Lancelotmay/BLETracker/src/ubx_messages_header.h

/***********************************************************
 *
 * Copyright (C) u-blox AG
 * u-blox AG, Thalwil, Switzerland
 *
 * All rights reserved.
 *
 * Permission to use, copy, modify, and distribute this software for any
 * purpose without fee is hereby granted, provided that this entire notice is
 * included in all copies of any software which is or includes a copy or
 * modification of this software and in all copies of the supporting
 * documentation for such software.
 *
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
 ***********************************************************
 *
 * Project:  Protocol Specification
 * Purpose:  Structure definitions for UBX messages
 * Audience: PUB
 *
 * This file is automatically generated!
 * Manual edits may be overwritten!
 *
 ***********************************************************/
/*!
	\file
	\brief UBX message definitions

*/

#ifndef __PROTO_UBX_STRUCT_DEF_H_479EEE3A_CC65683
#define __PROTO_UBX_STRUCT_DEF_H_479EEE3A_CC65683

#ifndef UBX_STANDARD_TYPES_DEFINED
/*----------------*/
/* Standard types */
/*----------------*/
typedef signed int			   I;   //!<  = I4
typedef unsigned int		   U;   //!<  = U4
typedef unsigned long		   BL;  //!<  = L4 (TRUE or FALSE only)
typedef	signed char			   I1;	//!<  signed 1 byte integer
typedef	signed short		   I2;	//!<  signed 2 byte integer
typedef	signed int			   I4;	//!<  signed 4 byte integer
typedef	signed long long int   I8;  //!<  signed 8 byte integer
typedef	unsigned char		   U1;	//!<  unsigned 1 byte integer
typedef	unsigned char		   X1;	//!<  unsigned 1 byte integer, to be interpreted as bitmask
typedef	unsigned short	       U2;	//!<  unsigned 2 byte integer
typedef	unsigned short		   X2;	//!<  unsigned 2 byte integer, to be interpreted as bitmask
typedef	unsigned int		   U4;	//!<  unsigned 4 byte integer
typedef	unsigned int		   X4;	//!<  unsigned 4 byte integer, to be interpreted as bitmask
typedef	unsigned long long int U8;	//!<  unsigned 8 byte integer
typedef	float				   R4;	//!<  4 byte floating point
typedef	double				   R8;	//!<  8 byte floating point
typedef	char				   CH;	//!<  ASCII character
typedef	unsigned char		   L1;	//!<  1 byte logical (TRUE or FALSE only)
typedef	unsigned short		   L2;	//!<  2 byte logical (TRUE or FALSE only)
typedef	unsigned int		   L4;	//!<  4 byte logical (TRUE or FALSE only)
typedef	unsigned int		    L;	//!<  4 byte logical (TRUE or FALSE only)

#define UBX_STANDARD_TYPES_DEFINED
#endif // ifndef UBX_STANDARD_TYPES_DEFINED

#ifndef TRUE
#define TRUE 1
#endif
#ifndef FALSE
#define FALSE 0
#endif

//! UBX Protocol Header
typedef struct UBX_HEAD_s
{
	U2 prefix;					//!< Prefix, always #UBX_PREFIX
	U1 class_id;					//!< UBX Class Id
	U1 msg_id;					//!< UBX Message Id
	U2 size;					//!< Payload Size
} UBX_HEAD_t, *UBX_HEAD_pt;

#define UBX_SYNC_CHAR_1 0xB5u    //!< First synchronization character of UBX Protocol
#define UBX_SYNC_CHAR_2 0x62u    //!< Second synchronization character of UBX Protocol
#define UBX_PREFIX      (UBX_SYNC_CHAR_2<<8|UBX_SYNC_CHAR_1) //!< UBX Protocol Prefix
#define UBX_PREFIX_SIZE 2u       //!< UBX Protocol Prefix Size in bytes
#define UBX_CHKSUM_SIZE 2u       //!< UBX Protocol Checksum Size in bytes

#define UBX_HEAD_SIZE sizeof(UBX_HEAD_t)                      //!< UBX Protocol Header Size
#define UBX_FRAME_SIZE (UBX_HEAD_SIZE+UBX_CHKSUM_SIZE) //!< Total size of the UBX Frame



//================================================================
//! ACK_ACK_DATA0: Output
/*!
Message Acknowledged
Output upon processing of an input message


This message's id is #UBXID_ACK_ACK
*/
//================================================================

typedef struct UBX_ACK_ACK_DATA0_s
{
	U1  clsID;                    //!< Class ID of the Acknowledged Message
	U1  msgID;                    //!< Message ID of the Acknowledged Message

} UBX_ACK_ACK_DATA0_t, *UBX_ACK_ACK_DATA0_pt;


#define UBXID_ACK_ACK 0x0501 //!< message id for ACK-ACK
	

//================================================================
//! ACK_NAK_DATA0: Output
/*!
Message Not-Acknowledged
Output upon processing of an input message


This message's id is #UBXID_ACK_NAK
*/
//================================================================

typedef struct UBX_ACK_NAK_DATA0_s
{
	U1  clsID;                    //!< Class ID of the Not-Acknowledged Message
	U1  msgID;                    //!< Message ID of the Not-Acknowledged Message

} UBX_ACK_NAK_DATA0_t, *UBX_ACK_NAK_DATA0_pt;


#define UBXID_ACK_NAK 0x0500 //!< message id for ACK-NAK
	

//================================================================
//! AID_ALM_POLL0: Poll Request
/*!
Poll GPS Aiding Almanac Data
Poll GPS Aiding Data (Almanac) for all 32 SVs by sending this message to the receiver without any payload. The receiver will return 32 messages of type AID-ALM as defined below.

   \note: All UBX-AID messages are deprecated; use UBX-MGA messages instead

This message's id is #UBXID_AID_ALM
*/
//================================================================

typedef struct UBX_AID_ALM_POLL0_s
{

} UBX_AID_ALM_POLL0_t, *UBX_AID_ALM_POLL0_pt;


#define UBXID_AID_ALM 0x0B30 //!< message id for AID-ALM
	

//================================================================
//! AID_ALM_POLLID: Poll Request
/*!
Poll GPS Aiding Almanac Data for a SV
Poll GPS Aiding Data (Almanac) for an SV by sending this message to the receiver. The receiver will return one message of type AID-ALM as defined below.

   \note: All UBX-AID messages are deprecated; use UBX-MGA messages instead

This message's id is #UBXID_AID_ALM
*/
//================================================================

typedef struct UBX_AID_ALM_POLLID_s
{
	U1  svid;                     //!< SV ID for which the receiver shall return its Almanac Data (Valid Range: 1 .. 32 or 51, 56, 63).

} UBX_AID_ALM_POLLID_t, *UBX_AID_ALM_POLLID_pt;


//#define UBXID_AID_ALM 0x0B30  // already defined, see above


//================================================================
//! AID_ALM_DATA0: Input/Output
/*!
GPS Aiding Almanac Input/Output Message
* If the WEEK Value is 0, DWRD0 to DWRD7 are not sent as the Almanac is not available for the given SV. This may happen even if NAV-SVINFO and RXM-SVSI are indicating almanac availability as the internal data may not represent the content of an original broadcast almanac (or only parts thereof).
* DWORD0 to DWORD7 contain the 8 words following the Hand-Over Word ( HOW ) from the GPS navigation message, either pages 1 to 24 of sub-frame 5 or pages 2 to 10 of subframe 4. See IS-GPS-200 for a full description of the contents of the Almanac pages.
* In DWORD0 to DWORD7, the parity bits have been removed, and the 24 bits of data are located in Bits 0 to 23. Bits 24 to 31 shall be ignored.
* Example: Parameter e (Eccentricity) from Almanac Subframe 4/5, Word 3, Bits 69-84 within the subframe can be found in DWRD0, Bits 15-0 whereas Bit 0 is the LSB.

   \note: All UBX-AID messages are deprecated; use UBX-MGA messages instead

This message's id is #UBXID_AID_ALM
*/
//================================================================

typedef struct UBX_AID_ALM_DATA0_s
{
	U4  svid;                     //!< SV ID for which this
	U4  week;                     //!< Issue Date of Almanac (GPS week number)
	//OPTIONAL: UBX_AID_ALM_DATA0_DWRD_t repeat0[0];              

} UBX_AID_ALM_DATA0_t, *UBX_AID_ALM_DATA0_pt;


//! Repeated Sub-Structure of #UBX_AID_ALM_DATA0_t
typedef struct UBX_AID_ALM_DATA0_DWRD_s
{
	U4  dwrd[8];                  //!< Almanac Words

} UBX_AID_ALM_DATA0_DWRD_t, *UBX_AID_ALM_DATA0_DWRD_pt;



//#define UBXID_AID_ALM 0x0B30  // already defined, see above


//================================================================
//! AID_AOP_POLL0: Poll Request
/*!
Poll AssistNow Autonomous data, all satellites
Poll <i>AssistNow Autonomous</i> aiding data for all GPS satellites by sending this empty message. The receiver will return an AID-AOP message (see definition below) for each GPS satellite for which data is available.

   \note: All UBX-AID messages are deprecated; use UBX-MGA messages instead

This message's id is #UBXID_AID_AOP
*/
//================================================================

typedef struct UBX_AID_AOP_POLL0_s
{

} UBX_AID_AOP_POLL0_t, *UBX_AID_AOP_POLL0_pt;


#define UBXID_AID_AOP 0x0B33 //!< message id for AID-AOP
	

//================================================================
//! AID_AOP_POLLID: Poll Request
/*!
Poll AssistNow Autonomous data, one GPS satellite
Poll the <i>AssistNow Autonomous</i> data for the specified GPS satellite. The receiver will return a AID-AOP message (see definition below) if data is available for the requested satellite.

   \note: All UBX-AID messages are deprecated; use UBX-MGA messages instead

This message's id is #UBXID_AID_AOP
*/
//================================================================

typedef struct UBX_AID_AOP_POLLID_s
{
	U1  svid;                     //!< GPS SV ID for which the data is requested (valid range: 1..32).

} UBX_AID_AOP_POLLID_t, *UBX_AID_AOP_POLLID_pt;


//#define UBXID_AID_AOP 0x0B33  // already defined, see above


//================================================================
//! AID_AOP_DATA2: Input/Output
/*!
AssistNow Autonomous data
If enabled, this message is output at irregular intervals. It is output whenever <i>AssistNow Autonomous</i> has produced new data for a satellite. Depending on the availability of the optional data the receiver will output either version of the message. If this message is polled using one of the two poll requests described above the receiver will send this message if AssistNow Autonomous data is available or the corresponding poll request message if no AssistNow Autonomous data is available for each satellite (i.e. svid 1..32). At the user's choice the optional data may be chopped from the payload of a previously polled message when sending the message back to the receiver. Sending a valid AID-AOP message to the receiver will automatically enable the <i>AssistNow Autonomous</i> feature on the receiver. See the section <r href=\"AOP-DESC'>AssistNow Autonomous</r> in the receiver description for details on this feature.

   \note: All UBX-AID messages are deprecated; use UBX-MGA messages instead

This message's id is #UBXID_AID_AOP
*/
//================================================================

typedef struct UBX_AID_AOP_DATA2_s
{
	U1  gnssId;                   //!< GNSS identifier (see <r href=\"DESC-SVNumbering-UBX'>Satellite Numbering</r>)
	U1  svId;                     //!< Satellite identifier (see <r href=\"DESC-SVNumbering-UBX'>Satellite Numbering</r>)
	U1  reserved1[2];             //!< <r href='DESC-UBX-Reserved'>Reserved</r>
	U1  data[64];                 //!< assistance data

} UBX_AID_AOP_DATA2_t, *UBX_AID_AOP_DATA2_pt;


//#define UBXID_AID_AOP 0x0B33  // already defined, see above


//================================================================
//! AID_EPH_POLL0: Poll Request
/*!
Poll GPS Aiding Ephemeris Data
Poll GPS Aiding Data (Ephemeris) for all 32 SVs by sending this message to the receiver without any payload. The receiver will return 32 messages of type AID-EPH as defined below.

   \note: All UBX-AID messages are deprecated; use UBX-MGA messages instead

This message's id is #UBXID_AID_EPH
*/
//================================================================

typedef struct UBX_AID_EPH_POLL0_s
{

} UBX_AID_EPH_POLL0_t, *UBX_AID_EPH_POLL0_pt;


#define UBXID_AID_EPH 0x0B31 //!< message id for AID-EPH
	

//================================================================
//! AID_EPH_POLLID: Poll Request
/*!
Poll GPS Aiding Ephemeris Data for a SV
Poll GPS Constellation Data (Ephemeris) for an SV by sending this message to the receiver. The receiver will return one message of type AID-EPH as defined below.

   \note: All UBX-AID messages are deprecated; use UBX-MGA messages instead

This message's id is #UBXID_AID_EPH
*/
//================================================================

typedef struct UBX_AID_EPH_POLLID_s
{
	U1  svid;                     //!< SV ID for which the receiver shall return its Ephemeris Data (Valid Range: 1 .. 32).

} UBX_AID_EPH_POLLID_t, *UBX_AID_EPH_POLLID_pt;


//#define UBXID_AID_EPH 0x0B31  // already defined, see above


//================================================================
//! AID_EPH_DATA0: Input/Output
/*!
GPS Aiding Ephemeris Input/Output Message
* SF1D0 to SF3D7 is only sent if ephemeris is available for this SV. If not, the payload may be reduced to 8 Bytes, or all bytes are set to zero, indicating that this SV Number does not have valid ephemeris for the moment. This may happen even if NAV-SVINFO and RXM-SVSI are indicating ephemeris availability as the internal data may not represent the content of an original broadcast ephemeris (or only parts thereof).
* SF1D0 to SF3D7 contain the 24 words following the Hand-Over Word ( HOW ) from the GPS navigation message, subframes 1 to 3. The Truncated TOW Count is not valid and cannot be used. See IS-GPS-200 for a full description of the contents of the Subframes.
* In SF1D0 to SF3D7, the parity bits have been removed, and the 24 bits of data are located in Bits 0 to 23. Bits 24 to 31 shall be ignored.
* When polled, the data contained in this message does not represent the full original ephemeris broadcast. Some fields that are irrelevant to u-blox receivers may be missing. The week number in Subframe 1 has already been modified to match the Time Of Ephemeris (TOE).

   \note: All UBX-AID messages are deprecated; use UBX-MGA messages instead

This message's id is #UBXID_AID_EPH
*/
//================================================================

typedef struct UBX_AID_EPH_DATA0_s
{
	U4  svid;                     //!< SV ID for which this ephemeris data is (Valid Range: 1 .. 32).
	U4  how;                      //!< Hand-Over Word of first Subframe. This is required if data is sent to the receiver.
	//OPTIONAL: UBX_AID_EPH_DATA0_SF1D_t repeat0[0];              

} UBX_AID_EPH_DATA0_t, *UBX_AID_EPH_DATA0_pt;


//! Repeated Sub-Structure of #UBX_AID_EPH_DATA0_t
typedef struct UBX_AID_EPH_DATA0_SF1D_s
{
	U4  sf1d[8];                  //!< Subframe 1 Words 3..10 (SF1D0..SF1D7)
	U4  sf2d[8];                  //!< Subframe 2 Words 3..10 (SF2D0..SF2D7)
	U4  sf3d[8];                  //!< Subframe 3 Words 3..10 (SF3D0..SF3D7)

} UBX_AID_EPH_DATA0_SF1D_t, *UBX_AID_EPH_DATA0_SF1D_pt;



//#define UBXID_AID_EPH 0x0B31  // already defined, see above


//================================================================
//! AID_HUI_POLL0: Poll Request
/*!
Poll GPS Health, UTC, ionosphere parameters
-

   \note: All UBX-AID messages are deprecated; use UBX-MGA messages instead

This message's id is #UBXID_AID_HUI
*/
//================================================================

typedef struct UBX_AID_HUI_POLL0_s
{

} UBX_AID_HUI_POLL0_t, *UBX_AID_HUI_POLL0_pt;


#define UBXID_AID_HUI 0x0B02 //!< message id for AID-HUI
	

//================================================================
//! AID_HUI_DATA1: Input/Output
/*!
GPS Health, UTC and ionosphere parameters
This message contains a health bit mask, UTC time and Klobuchar parameters. For more information on these parameters, see the ICD-GPS-200 documentation.

   \note: All UBX-AID messages are deprecated; use UBX-MGA messages instead

This message's id is #UBXID_AID_HUI
*/
//================================================================

typedef struct UBX_AID_HUI_DATA1_s
{
	X4  health;                   //!< Bitmask, every bit represenst a GPS SV (1-32). If the bit is set the SV is healthy.
	R8  utcA0;                    //!< UTC - parameter A0
	R8  utcA1;                    //!< UTC - parameter A1
	I4  utcTOW;                   //!< UTC - reference time of week
	I2  utcWNT;                   //!< UTC - reference week number
	I2  utcLS;                    //!< UTC - time difference due to leap seconds before event
	I2  utcWNF;                   //!< UTC - week number when next leap second event occurs
	I2  utcDN;                    //!< UTC - day of week when next leap second event occurs
	I2  utcLSF;                   //!< UTC - time difference due to leap seconds after event
	I2  utcSpare;                 //!< UTC - Spare to ensure structure is a multiple of 4 bytes
	R4  klobA0;                   //!< Klobuchar - alpha 0
	R4  klobA1;                   //!< Klobuchar - alpha 1
	R4  klobA2;                   //!< Klobuchar - alpha 2
	R4  klobA3;                   //!< Klobuchar - alpha 3
	R4  klobB0;                   //!< Klobuchar - beta 0
	R4  klobB1;                   //!< Klobuchar - beta 1
	R4  klobB2;                   //!< Klobuchar - beta 2
	R4  klobB3;                   //!< Klobuchar - beta 3
	X4  flags;                    //!< flags

} UBX_AID_HUI_DATA1_t, *UBX_AID_HUI_DATA1_pt;


//! \name Bit Definitions for #UBX_AID_HUI_DATA1_s::flags
//@{
#define UBX_AID_HUI_DATA1_FLAGS_HEALTHVALID_MASK 0x1  //!< Mask for field healthValid in bitmask flags
#define UBX_AID_HUI_DATA1_FLAGS_HEALTHVALID_GET(val)  (U)(((val)&UBX_AID_HUI_DATA1_FLAGS_HEALTHVALID_MASK)>>0)  //!< Get healthValid from bitmask flags
#define UBX_AID_HUI_DATA1_FLAGS_UTCVALID_MASK 0x2  //!< Mask for field utcValid in bitmask flags
#define UBX_AID_HUI_DATA1_FLAGS_UTCVALID_GET(val)  (U)(((val)&UBX_AID_HUI_DATA1_FLAGS_UTCVALID_MASK)>>1)  //!< Get utcValid from bitmask flags
#define UBX_AID_HUI_DATA1_FLAGS_KLOBVALID_MASK 0x4  //!< Mask for field klobValid in bitmask flags
#define UBX_AID_HUI_DATA1_FLAGS_KLOBVALID_GET(val)  (U)(((val)&UBX_AID_HUI_DATA1_FLAGS_KLOBVALID_MASK)>>2)  //!< Get klobValid from bitmask flags

//@}


//#define UBXID_AID_HUI 0x0B02  // already defined, see above


//================================================================
//! AID_INI_POLL0: Poll Request
/*!
Poll GPS Initial Aiding Data
-

   \note: All UBX-AID messages are deprecated; use UBX-MGA messages instead

This message's id is #UBXID_AID_INI
*/
//================================================================

typedef struct UBX_AID_INI_POLL0_s
{

} UBX_AID_INI_POLL0_t, *UBX_AID_INI_POLL0_pt;


#define UBXID_AID_INI 0x0B01 //!< message id for AID-INI
	

//================================================================
//! AID_INI_U6: Input/Output
/*!
Aiding position, time, frequency, clock drift
This message contains position, time and clock drift information. The position can be input in either the ECEF X/Y/Z coordinate system or as lat/lon/height. The time can either be input as inexact value via the standard communication interface, suffering from latency depending on the baud rate, or using hardware time synchronization where an accurate time pulse is input on the external interrupts. It is also possible to supply hardware frequency aiding by connecting a continuous signal to an external interrupt.

   \note: All UBX-AID messages are deprecated; use UBX-MGA messages instead

This message's id is #UBXID_AID_INI
*/
//================================================================

typedef struct UBX_AID_INI_U6_s
{
	I4  ecefXOrLat;               //!< WGS84 ECEF X coordinate or latitude, depending on flags below
	I4  ecefYOrLon;               //!< WGS84 ECEF Y coordinate or longitude, depending on flags below
	I4  ecefZOrAlt;               //!< WGS84 ECEF Z coordinate or altitude, depending on flags below
	U4  posAcc;                   //!< Position accuracy (stddev)
	X2  tmCfg;                    //!< Time mark configuration
	U2  wnoOrDate;                //!< Actual week number or yearSince2000/Month (YYMM), depending on flags below
	U4  towOrTime;                //!< Actual time of week or DayOfMonth/Hour/Minute/Second (DDHHMMSS), depending on flags below
	I4  towNs;                    //!< Fractional part of time of week
	U4  tAccMs;                   //!< Milliseconds part of time accuracy
	U4  tAccNs;                   //!< Nanoseconds part of time accuracy
	I4  clkDOrFreq;               //!< Clock drift or frequency, depending on flags below
	U4  clkDAccOrFreqAcc;         //!< Accuracy of clock drift or frequency, depending on flags below
	X4  flags;                    //!< Bitmask with the following flags

} UBX_AID_INI_U6_t, *UBX_AID_INI_U6_pt;


//! \name Bit Definitions for #UBX_AID_INI_U6_s::tmCfg
//@{
#define UBX_AID_INI_U6_TMCFG_FEDGE_MASK 0x02  //!< Mask for field fEdge in bitmask tmCfg
#define UBX_AID_INI_U6_TMCFG_FEDGE_GET(val)  (U)(((val)&UBX_AID_INI_U6_TMCFG_FEDGE_MASK)>>1)  //!< Get fEdge from bitmask tmCfg
#define UBX_AID_INI_U6_TMCFG_TM1_MASK 0x10  //!< Mask for field tm1 in bitmask tmCfg
#define UBX_AID_INI_U6_TMCFG_TM1_GET(val)  (U)(((val)&UBX_AID_INI_U6_TMCFG_TM1_MASK)>>4)  //!< Get tm1 from bitmask tmCfg
#define UBX_AID_INI_U6_TMCFG_F1_MASK 0x40  //!< Mask for field f1 in bitmask tmCfg
#define UBX_AID_INI_U6_TMCFG_F1_GET(val)  (U)(((val)&UBX_AID_INI_U6_TMCFG_F1_MASK)>>6)  //!< Get f1 from bitmask tmCfg

//@}
//! \name Bit Definitions for #UBX_AID_INI_U6_s::flags
//@{
#define UBX_AID_INI_U6_FLAGS_POS_MASK 0x01  //!< Mask for field pos in bitmask flags
#define UBX_AID_INI_U6_FLAGS_POS_GET(val)  (U)(((val)&UBX_AID_INI_U6_FLAGS_POS_MASK)>>0)  //!< Get pos from bitmask flags
#define UBX_AID_INI_U6_FLAGS_TIME_MASK 0x02  //!< Mask for field time in bitmask flags
#define UBX_AID_INI_U6_FLAGS_TIME_GET(val)  (U)(((val)&UBX_AID_INI_U6_FLAGS_TIME_MASK)>>1)  //!< Get time from bitmask flags
#define UBX_AID_INI_U6_FLAGS_CLOCKD_MASK 0x04  //!< Mask for field clockD in bitmask flags
#define UBX_AID_INI_U6_FLAGS_CLOCKD_GET(val)  (U)(((val)&UBX_AID_INI_U6_FLAGS_CLOCKD_MASK)>>2)  //!< Get clockD from bitmask flags
#define UBX_AID_INI_U6_FLAGS_TP_MASK 0x08  //!< Mask for field tp in bitmask flags
#define UBX_AID_INI_U6_FLAGS_TP_GET(val)  (U)(((val)&UBX_AID_INI_U6_FLAGS_TP_MASK)>>3)  //!< Get tp from bitmask flags
#define UBX_AID_INI_U6_FLAGS_CLOCKF_MASK 0x10  //!< Mask for field clockF in bitmask flags
#define UBX_AID_INI_U6_FLAGS_CLOCKF_GET(val)  (U)(((val)&UBX_AID_INI_U6_FLAGS_CLOCKF_MASK)>>4)  //!< Get clockF from bitmask flags
#define UBX_AID_INI_U6_FLAGS_LLA_MASK 0x20  //!< Mask for field lla in bitmask flags
#define UBX_AID_INI_U6_FLAGS_LLA_GET(val)  (U)(((val)&UBX_AID_INI_U6_FLAGS_LLA_MASK)>>5)  //!< Get lla from bitmask flags
#define UBX_AID_INI_U6_FLAGS_ALTINV_MASK 0x40  //!< Mask for field altInv in bitmask flags
#define UBX_AID_INI_U6_FLAGS_ALTINV_GET(val)  (U)(((val)&UBX_AID_INI_U6_FLAGS_ALTINV_MASK)>>6)  //!< Get altInv from bitmask flags
#define UBX_AID_INI_U6_FLAGS_PREVTM_MASK 0x80  //!< Mask for field prevTm in bitmask flags
#define UBX_AID_INI_U6_FLAGS_PREVTM_GET(val)  (U)(((val)&UBX_AID_INI_U6_FLAGS_PREVTM_MASK)>>7)  //!< Get prevTm from bitmask flags
#define UBX_AID_INI_U6_FLAGS_UTC_MASK 0x400  //!< Mask for field utc in bitmask flags
#define UBX_AID_INI_U6_FLAGS_UTC_GET(val)  (U)(((val)&UBX_AID_INI_U6_FLAGS_UTC_MASK)>>10)  //!< Get utc from bitmask flags

//@}


//#define UBXID_AID_INI 0x0B01  // already defined, see above


//================================================================
//! CFG_ANT_POLL0: Poll Request
/*!
Poll Antenna Control Settings
Sending this (empty / no-payload) message to the receiver results in the receiver returning a message of type CFG-ANT with a payload as defined below


This message's id is #UBXID_CFG_ANT
*/
//================================================================

typedef struct UBX_CFG_ANT_POLL0_s
{

} UBX_CFG_ANT_POLL0_t, *UBX_CFG_ANT_POLL0_pt;


#define UBXID_CFG_ANT 0x0613 //!< message id for CFG-ANT
	

//================================================================
//! CFG_ANT_DATA0: Input/Output
/*!
Antenna Control Settings
-


This message's id is #UBXID_CFG_ANT
*/
//================================================================

typedef struct UBX_CFG_ANT_DATA0_s
{
	X2  flags;                    //!< Antenna Flag Mask
	X2  pins;                     //!< Antenna Pin Configuration

} UBX_CFG_ANT_DATA0_t, *UBX_CFG_ANT_DATA0_pt;


//! \name Bit Definitions for #UBX_CFG_ANT_DATA0_s::flags
//@{
#define UBX_CFG_ANT_DATA0_FLAGS_SVCS_MASK 0x0001  //!< Mask for field svcs in bitmask flags
#define UBX_CFG_ANT_DATA0_FLAGS_SVCS_GET(val)  (U)(((val)&UBX_CFG_ANT_DATA0_FLAGS_SVCS_MASK)>>0)  //!< Get svcs from bitmask flags
#define UBX_CFG_ANT_DATA0_FLAGS_SCD_MASK 0x0002  //!< Mask for field scd in bitmask flags
#define UBX_CFG_ANT_DATA0_FLAGS_SCD_GET(val)  (U)(((val)&UBX_CFG_ANT_DATA0_FLAGS_SCD_MASK)>>1)  //!< Get scd from bitmask flags
#define UBX_CFG_ANT_DATA0_FLAGS_OCD_MASK 0x0004  //!< Mask for field ocd in bitmask flags
#define UBX_CFG_ANT_DATA0_FLAGS_OCD_GET(val)  (U)(((val)&UBX_CFG_ANT_DATA0_FLAGS_OCD_MASK)>>2)  //!< Get ocd from bitmask flags
#define UBX_CFG_ANT_DATA0_FLAGS_PDWNONSCD_MASK 0x0008  //!< Mask for field pdwnOnSCD in bitmask flags
#define UBX_CFG_ANT_DATA0_FLAGS_PDWNONSCD_GET(val)  (U)(((val)&UBX_CFG_ANT_DATA0_FLAGS_PDWNONSCD_MASK)>>3)  //!< Get pdwnOnSCD from bitmask flags
#define UBX_CFG_ANT_DATA0_FLAGS_RECOVERY_MASK 0x0010  //!< Mask for field recovery in bitmask flags
#define UBX_CFG_ANT_DATA0_FLAGS_RECOVERY_GET(val)  (U)(((val)&UBX_CFG_ANT_DATA0_FLAGS_RECOVERY_MASK)>>4)  //!< Get recovery from bitmask flags

//@}
//! \name Bit Definitions for #UBX_CFG_ANT_DATA0_s::pins
//@{
#define UBX_CFG_ANT_DATA0_PINS_PINSWITCH_MASK 0x001F  //!< Mask for field pinSwitch in bitmask pins
#define UBX_CFG_ANT_DATA0_PINS_PINSWITCH_GET(val)  (U)(((val)&UBX_CFG_ANT_DATA0_PINS_PINSWITCH_MASK)>>0)  //!< Get pinSwitch from bitmask pins
#define UBX_CFG_ANT_DATA0_PINS_PINSCD_MASK 0x03E0  //!< Mask for field pinSCD in bitmask pins
#define UBX_CFG_ANT_DATA0_PINS_PINSCD_GET(val)  (U)(((val)&UBX_CFG_ANT_DATA0_PINS_PINSCD_MASK)>>5)  //!< Get pinSCD from bitmask pins
#define UBX_CFG_ANT_DATA0_PINS_PINOCD_MASK 0x7C00  //!< Mask for field pinOCD in bitmask pins
#define UBX_CFG_ANT_DATA0_PINS_PINOCD_GET(val)  (U)(((val)&UBX_CFG_ANT_DATA0_PINS_PINOCD_MASK)>>10)  //!< Get pinOCD from bitmask pins
#define UBX_CFG_ANT_DATA0_PINS_RECONFIG_MASK 0x8000  //!< Mask for field reconfig in bitmask pins
#define UBX_CFG_ANT_DATA0_PINS_RECONFIG_GET(val)  (U)(((val)&UBX_CFG_ANT_DATA0_PINS_RECONFIG_MASK)>>15)  //!< Get reconfig from bitmask pins

//@}


//#define UBXID_CFG_ANT 0x0613  // already defined, see above


//================================================================
//! CFG_CFG_U5: Command
/*!
Clear, Save and Load configurations
See <r href=\"CFG-CFG-DESC'>Receiver Configuration</r> for a detailed description on how Receiver Configuration should be used. The three masks are made up of individual bits, each bit indicating the sub-section of all configurations on which the corresponding action shall be carried out. The reserved bits in the masks must be set to '0'. For detailed information refer to the <r href=\"orgConfigSect'>Organization of the Configuration Sections</r>. Note that commands can be combined. The sequence of execution is Clear, Save, Load


This message's id is #UBXID_CFG_CFG
*/
//================================================================

typedef struct UBX_CFG_CFG_U5_s
{
	X4  clearMask;                //!< Mask with configuration sub-sections to clear (i.e. load default configurations to permanent configurations in non-volatile memory)
	X4  saveMask;                 //!< Mask with configuration sub-sections to save (i.e. save current configurations to non-volatile memory), see ID description of clearMask
	X4  loadMask;                 //!< Mask with configuration sub-sections to load (i.e. load permanent configurations from non-volatile memory to current configurations), see ID description of clearMask
	//OPTIONAL: UBX_CFG_CFG_U5_DEVICEMASK_t repeat0[0];              

} UBX_CFG_CFG_U5_t, *UBX_CFG_CFG_U5_pt;


//! \name Bit Definitions for #UBX_CFG_CFG_U5_s::clearMask
//@{
#define UBX_CFG_CFG_U5_CLEARMASK_IOPORT_MASK 0x0001  //!< Mask for field ioPort in bitmask clearMask
#define UBX_CFG_CFG_U5_CLEARMASK_IOPORT_GET(val)  (U)(((val)&UBX_CFG_CFG_U5_CLEARMASK_IOPORT_MASK)>>0)  //!< Get ioPort from bitmask clearMask
#define UBX_CFG_CFG_U5_CLEARMASK_MSGCONF_MASK 0x0002  //!< Mask for field msgConf in bitmask clearMask
#define UBX_CFG_CFG_U5_CLEARMASK_MSGCONF_GET(val)  (U)(((val)&UBX_CFG_CFG_U5_CLEARMASK_MSGCONF_MASK)>>1)  //!< Get msgConf from bitmask clearMask
#define UBX_CFG_CFG_U5_CLEARMASK_INFMSG_MASK 0x0004  //!< Mask for field infMsg in bitmask clearMask
#define UBX_CFG_CFG_U5_CLEARMASK_INFMSG_GET(val)  (U)(((val)&UBX_CFG_CFG_U5_CLEARMASK_INFMSG_MASK)>>2)  //!< Get infMsg from bitmask clearMask
#define UBX_CFG_CFG_U5_CLEARMASK_NAVCONF_MASK 0x0008  //!< Mask for field navConf in bitmask clearMask
#define UBX_CFG_CFG_U5_CLEARMASK_NAVCONF_GET(val)  (U)(((val)&UBX_CFG_CFG_U5_CLEARMASK_NAVCONF_MASK)>>3)  //!< Get navConf from bitmask clearMask
#define UBX_CFG_CFG_U5_CLEARMASK_RXMCONF_MASK 0x0010  //!< Mask for field rxmConf in bitmask clearMask
#define UBX_CFG_CFG_U5_CLEARMASK_RXMCONF_GET(val)  (U)(((val)&UBX_CFG_CFG_U5_CLEARMASK_RXMCONF_MASK)>>4)  //!< Get rxmConf from bitmask clearMask
#define UBX_CFG_CFG_U5_CLEARMASK_RINVCONF_MASK 0x0200  //!< Mask for field rinvConf in bitmask clearMask
#define UBX_CFG_CFG_U5_CLEARMASK_RINVCONF_GET(val)  (U)(((val)&UBX_CFG_CFG_U5_CLEARMASK_RINVCONF_MASK)>>9)  //!< Get rinvConf from bitmask clearMask
#define UBX_CFG_CFG_U5_CLEARMASK_ANTCONF_MASK 0x0400  //!< Mask for field antConf in bitmask clearMask
#define UBX_CFG_CFG_U5_CLEARMASK_ANTCONF_GET(val)  (U)(((val)&UBX_CFG_CFG_U5_CLEARMASK_ANTCONF_MASK)>>10)  //!< Get antConf from bitmask clearMask
#define UBX_CFG_CFG_U5_CLEARMASK_LOGCONF_MASK 0x0800  //!< Mask for field logConf in bitmask clearMask
#define UBX_CFG_CFG_U5_CLEARMASK_LOGCONF_GET(val)  (U)(((val)&UBX_CFG_CFG_U5_CLEARMASK_LOGCONF_MASK)>>11)  //!< Get logConf from bitmask clearMask
#define UBX_CFG_CFG_U5_CLEARMASK_FTSCONF_MASK 0x1000  //!< Mask for field ftsConf in bitmask clearMask
#define UBX_CFG_CFG_U5_CLEARMASK_FTSCONF_GET(val)  (U)(((val)&UBX_CFG_CFG_U5_CLEARMASK_FTSCONF_MASK)>>12)  //!< Get ftsConf from bitmask clearMask

//@}


//! Repeated Sub-Structure of #UBX_CFG_CFG_U5_t
typedef struct UBX_CFG_CFG_U5_DEVICEMASK_s
{
	X1  deviceMask;               //!< Mask which selects the memory devices for this command.

} UBX_CFG_CFG_U5_DEVICEMASK_t, *UBX_CFG_CFG_U5_DEVICEMASK_pt;

//! \name Bit Definitions for #UBX_CFG_CFG_U5_DEVICEMASK_s::deviceMask
//@{
#define UBX_CFG_CFG_U5_DEVICEMASK_DEVICEMASK_DEVBBR_MASK 0x01  //!< Mask for field devBBR in bitmask deviceMask
#define UBX_CFG_CFG_U5_DEVICEMASK_DEVICEMASK_DEVBBR_GET(val)  (U)(((val)&UBX_CFG_CFG_U5_DEVICEMASK_DEVICEMASK_DEVBBR_MASK)>>0)  //!< Get devBBR from bitmask deviceMask
#define UBX_CFG_CFG_U5_DEVICEMASK_DEVICEMASK_DEVFLASH_MASK 0x02  //!< Mask for field devFlash in bitmask deviceMask
#define UBX_CFG_CFG_U5_DEVICEMASK_DEVICEMASK_DEVFLASH_GET(val)  (U)(((val)&UBX_CFG_CFG_U5_DEVICEMASK_DEVICEMASK_DEVFLASH_MASK)>>1)  //!< Get devFlash from bitmask deviceMask
#define UBX_CFG_CFG_U5_DEVICEMASK_DEVICEMASK_DEVEEPROM_MASK 0x04  //!< Mask for field devEEPROM in bitmask deviceMask
#define UBX_CFG_CFG_U5_DEVICEMASK_DEVICEMASK_DEVEEPROM_GET(val)  (U)(((val)&UBX_CFG_CFG_U5_DEVICEMASK_DEVICEMASK_DEVEEPROM_MASK)>>2)  //!< Get devEEPROM from bitmask deviceMask
#define UBX_CFG_CFG_U5_DEVICEMASK_DEVICEMASK_DEVSPIFLASH_MASK 0x10  //!< Mask for field devSpiFlash in bitmask deviceMask
#define UBX_CFG_CFG_U5_DEVICEMASK_DEVICEMASK_DEVSPIFLASH_GET(val)  (U)(((val)&UBX_CFG_CFG_U5_DEVICEMASK_DEVICEMASK_DEVSPIFLASH_MASK)>>4)  //!< Get devSpiFlash from bitmask deviceMask

//@}


#define UBXID_CFG_CFG 0x0609 //!< message id for CFG-CFG
	

//================================================================
//! CFG_DAT_POLL0: Poll Request
/*!
Poll Datum Setting
Upon sending of this message, the receiver returns CFG-DAT as defined below


This message's id is #UBXID_CFG_DAT
*/
//================================================================

typedef struct UBX_CFG_DAT_POLL0_s
{

} UBX_CFG_DAT_POLL0_t, *UBX_CFG_DAT_POLL0_pt;


#define UBXID_CFG_DAT 0x0606 //!< message id for CFG-DAT
	

//================================================================
//! CFG_DAT_SETCUSTOM: Input
/*!
Set User-defined Datum
-


This message's id is #UBXID_CFG_DAT
*/
//================================================================

typedef struct UBX_CFG_DAT_SETCUSTOM_s
{
	R8  majA;                     //!< Semi-major Axis ( accepted range = 6,300,000.0 to 6,500,000.0 meters ).
	R8  flat;                     //!< 1.0 / Flattening ( accepted range is 0.0 to 500.0 ).
	R4  dX;                       //!< X Axis shift at the origin ( accepted range is +/- 5000.0 meters ).
	R4  dY;                       //!< Y Axis shift at the origin ( accepted range is +/- 5000.0 meters ).
	R4  dZ;                       //!< Z Axis shift at the origin ( accepted range is +/- 5000.0 meters ).
	R4  rotX;                     //!< Rotation about the X Axis ( accepted range is +/- 20.0 milli-arc seconds ).
	R4  rotY;                     //!< Rotation about the Y Axis ( accepted range is +/- 20.0 milli-arc seconds ).
	R4  rotZ;                     //!< Rotation about the Z Axis ( accepted range is +/- 20.0 milli-arc seconds ).
	R4  scale;                    //!< Scale change ( accepted range is 0.0 to 50.0 parts per million ).

} UBX_CFG_DAT_SETCUSTOM_t, *UBX_CFG_DAT_SETCUSTOM_pt;


//#define UBXID_CFG_DAT 0x0606  // already defined, see above


//================================================================
//! CFG_DAT_GETCURRENT: Output
/*!
The currently defined Datum
Returns the parameters of the currently defined datum. If no user-defined datum has been set, this will default to WGS84.


This message's id is #UBXID_CFG_DAT
*/
//================================================================

typedef struct UBX_CFG_DAT_GETCURRENT_s
{
	U2  datumNum;                 //!< Datum Number: 0 = WGS84, -1 = user-defined
	CH  datumName[6];             //!< ASCII String: WGS84 or USER
	R8  majA;                     //!< Semi-major Axis ( accepted range = 6,300,000.0 to 6,500,000.0 meters ).
	R8  flat;                     //!< 1.0 / Flattening ( accepted range is 0.0 to 500.0 ).
	R4  dX;                       //!< X Axis shift at the origin ( accepted range is +/- 5000.0 meters ).
	R4  dY;                       //!< Y Axis shift at the origin ( accepted range is +/- 5000.0 meters ).
	R4  dZ;                       //!< Z Axis shift at the origin ( accepted range is +/- 5000.0 meters ).
	R4  rotX;                     //!< Rotation about the X Axis ( accepted range is +/- 20.0 milli-arc seconds ).
	R4  rotY;                     //!< Rotation about the Y Axis ( accepted range is +/- 20.0 milli-arc seconds ).
	R4  rotZ;                     //!< Rotation about the Z Axis ( accepted range is +/- 20.0 milli-arc seconds ).
	R4  scale;                    //!< Scale change ( accepted range is 0.0 to 50.0 parts per million ).

} UBX_CFG_DAT_GETCURRENT_t, *UBX_CFG_DAT_GETCURRENT_pt;


//#define UBXID_CFG_DAT 0x0606  // already defined, see above


//================================================================
//! CFG_DOSC_POLL0: Poll Request
/*!
Poll DOSC settings
Sending this message to the receiver results in the receiver returning a message of type CFG-DOSC-DATA0 with a payload as defined below for the oscillator specified


This message's id is #UBXID_CFG_DOSC
*/
//================================================================

typedef struct UBX_CFG_DOSC_POLL0_s
{

} UBX_CFG_DOSC_POLL0_t, *UBX_CFG_DOSC_POLL0_pt;


#define UBXID_CFG_DOSC 0x0661 //!< message id for CFG-DOSC
	

//================================================================
//! CFG_DOSC_DATA0: Get/Set
/*!
Disciplined oscillator configuration
This message allows the characteristics of the internal or external oscillator to be described to the receiver.
The gainVco and gainUncertainty parameters are normally set using the <r href=\"FTS-calib'>calibration process</r> initiated using <rc href=\"UBX-TIM-VCOCAL'>UBX-TIM-VCOCAL</rc>.
The behavior of the system can be badly affected by setting the wrong values, so customers are advised to only change these parameters with care.


This message's id is #UBXID_CFG_DOSC
*/
//================================================================

typedef struct UBX_CFG_DOSC_DATA0_s
{
	U1  version;                  //!< Message version (0 for this version)
	U1  numOsc;                   //!< Number of oscillators to configure (affects length of this message)
	U1  reserved1[2];             //!< <r href='DESC-UBX-Reserved'>Reserved</r>
	//REPEAT: UBX_CFG_DOSC_DATA0_OSCID_t repeat0[numOsc];         

} UBX_CFG_DOSC_DATA0_t, *UBX_CFG_DOSC_DATA0_pt;


//! Optional Sub-Structure of #UBX_CFG_DOSC_DATA0_t
typedef struct UBX_CFG_DOSC_DATA0_OSCID_s
{
	U1  oscId;                    //!< Id of oscillator.
	U1  reserved2;                //!< <r href='DESC-UBX-Reserved'>Reserved</r>
	X2  flags;                    //!< flags
	U4  freq;                     //!< Nominal frequency of source
	I4  phaseOffset;              //!< Intended phase offset of the oscillator relative to the leading edge of the time pulse
	U4  withTemp;                 //!< Oscillator stability limit over operating temperature range (must be > 0)
	U4  withAge;                  //!< Oscillator stability with age (must be > 0)
	U2  timeToTemp;               //!< The minimum time that it could take for a temperature variation to move the oscillator frequency by 'withTemp' (must be > 0)
	U1  reserved3[2];             //!< <r href='DESC-UBX-Reserved'>Reserved</r>
	I4  gainVco;                  //!< Oscillator control gain/slope; change of frequency per unit change in raw control change
	U1  gainUncertainty;          //!< Relative uncertainty (1 standard deviation) of oscillator control gain/slope
	U1  reserved4[3];             //!< <r href='DESC-UBX-Reserved'>Reserved</r>

} UBX_CFG_DOSC_DATA0_OSCID_t, *UBX_CFG_DOSC_DATA0_OSCID_pt;

//! \name Bit Definitions for #UBX_CFG_DOSC_DATA0_OSCID_s::flags
//@{
#define UBX_CFG_DOSC_DATA0_OSCID_FLAGS_ISCALIBRATED_MASK 0x0001  //!< Mask for field isCalibrated in bitmask flags
#define UBX_CFG_DOSC_DATA0_OSCID_FLAGS_ISCALIBRATED_GET(val)  (U)(((val)&UBX_CFG_DOSC_DATA0_OSCID_FLAGS_ISCALIBRATED_MASK)>>0)  //!< Get isCalibrated from bitmask flags
#define UBX_CFG_DOSC_DATA0_OSCID_FLAGS_CONTROLIF_MASK 0x001E  //!< Mask for field controlIf in bitmask flags
#define UBX_CFG_DOSC_DATA0_OSCID_FLAGS_CONTROLIF_GET(val)  (U)(((val)&UBX_CFG_DOSC_DATA0_OSCID_FLAGS_CONTROLIF_MASK)>>1)  //!< Get controlIf from bitmask flags

//@}


//#define UBXID_CFG_DOSC 0x0661  // already defined, see above


//================================================================
//! CFG_ESRC_POLL0: Poll Request
/*!
Poll ESRC settings
-


This message's id is #UBXID_CFG_ESRC
*/
//================================================================

typedef struct UBX_CFG_ESRC_POLL0_s
{

} UBX_CFG_ESRC_POLL0_t, *UBX_CFG_ESRC_POLL0_pt;


#define UBXID_CFG_ESRC 0x0660 //!< message id for CFG-ESRC
	

//================================================================
//! CFG_ESRC_DATA0: Get/Set
/*!
External synchronization source configuration
External time or frequency source configuration. The stability of time and frequency sources is described using different fields, see sourceType field documentation.


This message's id is #UBXID_CFG_ESRC
*/
//================================================================

typedef struct UBX_CFG_ESRC_DATA0_s
{
	U1  version;                  //!< Message version (0 for this version)
	U1  numSources;               //!< Number of sources (affects length of this message)
	U1  reserved1[2];             //!< <r href='DESC-UBX-Reserved'>Reserved</r>
	//REPEAT: UBX_CFG_ESRC_DATA0_EXTINT_t repeat0[numSources];     

} UBX_CFG_ESRC_DATA0_t, *UBX_CFG_ESRC_DATA0_pt;


//! Optional Sub-Structure of #UBX_CFG_ESRC_DATA0_t
typedef struct UBX_CFG_ESRC_DATA0_EXTINT_s
{
	U1  extInt;                   //!< EXTINT index of this source (0 for EXTINT0 and 1 for EXTINT1)
	U1  sourceType;               //!< Source type:
	X2  flags;                    //!< Flags
	U4  freq;                     //!< Nominal frequency of source
	U1  reserved2[4];             //!< <r href='DESC-UBX-Reserved'>Reserved</r>
	U4  withTemp;                 //!< Oscillator stability limit over operating temperature range (must be > 0)
	U4  withAge;                  //!< Oscillator stability with age (must be > 0)
	U2  timeToTemp;               //!< The minimum time that it could take for a temperature variation to move the oscillator frequency by 'withTemp' (must be > 0)
	U2  maxDevLifeTime;           //!< Maximum frequency deviation during lifetime (must be > 0)
	I4  offset;                   //!< Phase offset of signal
	U4  offsetUncertainty;        //!< Uncertainty of phase offset (one standard deviation)
	U4  jitter;                   //!< Phase jitter (must be > 0)

} UBX_CFG_ESRC_DATA0_EXTINT_t, *UBX_CFG_ESRC_DATA0_EXTINT_pt;

//! \name Bit Definitions for #UBX_CFG_ESRC_DATA0_EXTINT_s::flags
//@{
#define UBX_CFG_ESRC_DATA0_EXTINT_FLAGS_POLARITY_MASK 0x01  //!< Mask for field polarity in bitmask flags
#define UBX_CFG_ESRC_DATA0_EXTINT_FLAGS_POLARITY_GET(val)  (U)(((val)&UBX_CFG_ESRC_DATA0_EXTINT_FLAGS_POLARITY_MASK)>>0)  //!< Get polarity from bitmask flags
#define UBX_CFG_ESRC_DATA0_EXTINT_FLAGS_GNSSUTC_MASK 0x02  //!< Mask for field gnssUtc in bitmask flags
#define UBX_CFG_ESRC_DATA0_EXTINT_FLAGS_GNSSUTC_GET(val)  (U)(((val)&UBX_CFG_ESRC_DATA0_EXTINT_FLAGS_GNSSUTC_MASK)>>1)  //!< Get gnssUtc from bitmask flags

//@}


//#define UBXID_CFG_ESRC 0x0660  // already defined, see above


//================================================================
//! CFG_GNSS_POLL0: Poll Request
/*!
Poll the GNSS system configuration
Polls the configuration of the GNSS system configuration


This message's id is #UBXID_CFG_GNSS
*/
//================================================================

typedef struct UBX_CFG_GNSS_POLL0_s
{

} UBX_CFG_GNSS_POLL0_t, *UBX_CFG_GNSS_POLL0_pt;


#define UBXID_CFG_GNSS 0x063E //!< message id for CFG-GNSS
	

//================================================================
//! CFG_GNSS_DATA0: Input/Output
/*!
GNSS system configuration
Gets or sets the GNSS system channel sharing configuration.
If the receiver is sent a valid new configuration, it will respond with a <rc href=\"UBX-ACK-ACK'>UBX-ACK-ACK</rc> message and immediately change to the new configuration. Otherwise the receiver will reject the request, by issuing a <rc href=\"UBX-ACK-NAK'>UBX-ACK-NAK</rc> and continuing operation with the previous configuration.
The number of tracking channels in use must not exceed the number of tracking channels available in hardware, and the sum of all reserved tracking channels needs to be less than or equal to the number of tracking channels in use. Additionally, the maximum number of tracking channels used for the specific GNSS system must be greater or equal to the number of reserved tracking channels.
See section <r href=\"CFG-GNSS-DESC'>GNSS Configuration</r> for a discussion of the use of this message and section <r href=\"DESC-SVNumbering-UBX'>Satellite Numbering</r> for a description of the GNSS IDs available.
Configuration specific to the GNSS system can be done via other messages (e.g. <rc href=\"UBX-CFG-SBAS'>UBX-CFG-SBAS</rc>).
Note that GLONASS or BeiDou operation cannot be selected when the receiver is configured to operate in Power Save Mode (using <rc href=\"UBX-CFG-RXM'>UBX-CFG-RXM</rc>).
GPS and QZSS should always be either both enabled or both disabled.


This message's id is #UBXID_CFG_GNSS
*/
//================================================================

typedef struct UBX_CFG_GNSS_DATA0_s
{
	U1  msgVer;                   //!< Message version (=0 for this version)
	U1  numTrkChHw;               //!< Number of tracking channels available in hardware (read only)
	U1  numTrkChUse;              //!< Number of tracking channels to use (<= numTrkChHw)
	U1  numConfigBlocks;          //!< Number of configuration blocks following
	//REPEAT: UBX_CFG_GNSS_DATA0_GNSSID_t repeat0[numConfigBlocks];

} UBX_CFG_GNSS_DATA0_t, *UBX_CFG_GNSS_DATA0_pt;


//! Optional Sub-Structure of #UBX_CFG_GNSS_DATA0_t
typedef struct UBX_CFG_GNSS_DATA0_GNSSID_s
{
	U1  gnssId;                   //!< GNSS identifier (see <r href=\"DESC-SVNumbering-UBX'>Satellite Numbering</r>)
	U1  resTrkCh;                 //!< Number of reserved (minimum) tracking channels for this GNSS system
	U1  maxTrkCh;                 //!< Maximum number of tracking channels used for this GNSS system (>=resTrkChn)
	U1  reserved1;                //!< <r href='DESC-UBX-Reserved'>Reserved</r>
	X4  flags;                    //!< bitfield of flags

} UBX_CFG_GNSS_DATA0_GNSSID_t, *UBX_CFG_GNSS_DATA0_GNSSID_pt;

//! \name Bit Definitions for #UBX_CFG_GNSS_DATA0_GNSSID_s::flags
//@{
#define UBX_CFG_GNSS_DATA0_GNSSID_FLAGS_ENABLE_MASK 0x00000001  //!< Mask for field enable in bitmask flags
#define UBX_CFG_GNSS_DATA0_GNSSID_FLAGS_ENABLE_GET(val)  (U)(((val)&UBX_CFG_GNSS_DATA0_GNSSID_FLAGS_ENABLE_MASK)>>0)  //!< Get enable from bitmask flags
#define UBX_CFG_GNSS_DATA0_GNSSID_FLAGS_SIGCFGMASK_MASK 0x00FF0000  //!< Mask for field sigCfgMask in bitmask flags
#define UBX_CFG_GNSS_DATA0_GNSSID_FLAGS_SIGCFGMASK_GET(val)  (U)(((val)&UBX_CFG_GNSS_DATA0_GNSSID_FLAGS_SIGCFGMASK_MASK)>>16)  //!< Get sigCfgMask from bitmask flags

//@}


//#define UBXID_CFG_GNSS 0x063E  // already defined, see above


//================================================================
//! CFG_INF_POLLID: Poll Request
/*!
Poll configuration for one protocol
-


This message's id is #UBXID_CFG_INF
*/
//================================================================

typedef struct UBX_CFG_INF_POLLID_s
{
	U1  protocolID;               //!< Protocol Identifier, identifying the output protocol for this Poll Request. The following are valid Protocol Identifiers:

} UBX_CFG_INF_POLLID_t, *UBX_CFG_INF_POLLID_pt;


#define UBXID_CFG_INF 0x0602 //!< message id for CFG-INF
	

//================================================================
//! CFG_INF_DATA1: Input/Output
/*!
Information message configuration
The value of infMsgMask[x] below are that each bit represents one of the INF class messages (Bit 0 for ERROR, Bit 1 for WARNING and so on.). For a complete list, see the <rc href=\"UBX-INF'>Message Class INF</rc>. Several configurations can be concatenated to one input message. In this case the payload length can be a multiple of the normal length. Output messages from the module contain only one configuration unit. Note that I/O Ports 1 and 2 correspond to serial ports 1 and 2. I/O port 0 is DDC. I/O port 3 is USB. I/O port 4 is SPI. I/O port 5 is reserved for future use.


This message's id is #UBXID_CFG_INF
*/
//================================================================

typedef struct UBX_CFG_INF_DATA1_s
{
	//REPEAT: UBX_CFG_INF_DATA1_PROTOCOLID_t repeat0[N];              

} UBX_CFG_INF_DATA1_t, *UBX_CFG_INF_DATA1_pt;


//! Optional Sub-Structure of #UBX_CFG_INF_DATA1_t
typedef struct UBX_CFG_INF_DATA1_PROTOCOLID_s
{
	U1  protocolID;               //!< Protocol Identifier, identifying for which protocol the configuration is set/get. The following are valid Protocol Identifiers:
	U1  reserved1[3];             //!< <r href='DESC-UBX-Reserved'>Reserved</r>
	X1  infMsgMask[6];            //!< A bit mask, saying which information messages are enabled on each I/O port

} UBX_CFG_INF_DATA1_PROTOCOLID_t, *UBX_CFG_INF_DATA1_PROTOCOLID_pt;

//! \name Bit Definitions for #UBX_CFG_INF_DATA1_PROTOCOLID_s::infMsgMask
//@{
#define UBX_CFG_INF_DATA1_PROTOCOLID_INFMSGMASK_ERROR_MASK 0x01  //!< Mask for field ERROR in bitmask infMsgMask
#define UBX_CFG_INF_DATA1_PROTOCOLID_INFMSGMASK_ERROR_GET(val)  (U)(((val)&UBX_CFG_INF_DATA1_PROTOCOLID_INFMSGMASK_ERROR_MASK)>>0)  //!< Get ERROR from bitmask infMsgMask
#define UBX_CFG_INF_DATA1_PROTOCOLID_INFMSGMASK_WARNING_MASK 0x02  //!< Mask for field WARNING in bitmask infMsgMask
#define UBX_CFG_INF_DATA1_PROTOCOLID_INFMSGMASK_WARNING_GET(val)  (U)(((val)&UBX_CFG_INF_DATA1_PROTOCOLID_INFMSGMASK_WARNING_MASK)>>1)  //!< Get WARNING from bitmask infMsgMask
#define UBX_CFG_INF_DATA1_PROTOCOLID_INFMSGMASK_NOTICE_MASK 0x04  //!< Mask for field NOTICE in bitmask infMsgMask
#define UBX_CFG_INF_DATA1_PROTOCOLID_INFMSGMASK_NOTICE_GET(val)  (U)(((val)&UBX_CFG_INF_DATA1_PROTOCOLID_INFMSGMASK_NOTICE_MASK)>>2)  //!< Get NOTICE from bitmask infMsgMask
#define UBX_CFG_INF_DATA1_PROTOCOLID_INFMSGMASK_TEST_MASK 0x08  //!< Mask for field TEST in bitmask infMsgMask
#define UBX_CFG_INF_DATA1_PROTOCOLID_INFMSGMASK_TEST_GET(val)  (U)(((val)&UBX_CFG_INF_DATA1_PROTOCOLID_INFMSGMASK_TEST_MASK)>>3)  //!< Get TEST from bitmask infMsgMask
#define UBX_CFG_INF_DATA1_PROTOCOLID_INFMSGMASK_DEBUG_MASK 0x10  //!< Mask for field DEBUG in bitmask infMsgMask
#define UBX_CFG_INF_DATA1_PROTOCOLID_INFMSGMASK_DEBUG_GET(val)  (U)(((val)&UBX_CFG_INF_DATA1_PROTOCOLID_INFMSGMASK_DEBUG_MASK)>>4)  //!< Get DEBUG from bitmask infMsgMask

//@}


//#define UBXID_CFG_INF 0x0602  // already defined, see above


//================================================================
//! CFG_ITFM_POLL0: Poll Request
/*!
Poll Jamming/Interference Monitor configuration
-


This message's id is #UBXID_CFG_ITFM
*/
//================================================================

typedef struct UBX_CFG_ITFM_POLL0_s
{

} UBX_CFG_ITFM_POLL0_t, *UBX_CFG_ITFM_POLL0_pt;


#define UBXID_CFG_ITFM 0x0639 //!< message id for CFG-ITFM
	

//================================================================
//! CFG_ITFM_DATA0: Command
/*!
Jamming/Interference Monitor configuration
Configuration of Jamming/Interference monitor.


This message's id is #UBXID_CFG_ITFM
*/
//================================================================

typedef struct UBX_CFG_ITFM_DATA0_s
{
	X4  config;                   //!< interference config word.
	X4  config2;                  //!< extra settings for jamming/interference monitor

} UBX_CFG_ITFM_DATA0_t, *UBX_CFG_ITFM_DATA0_pt;


//! \name Bit Definitions for #UBX_CFG_ITFM_DATA0_s::config
//@{
#define UBX_CFG_ITFM_DATA0_CONFIG_BBTHRESHOLD_MASK 0x0000000F  //!< Mask for field bbThreshold in bitmask config
#define UBX_CFG_ITFM_DATA0_CONFIG_BBTHRESHOLD_GET(val)  (U)(((val)&UBX_CFG_ITFM_DATA0_CONFIG_BBTHRESHOLD_MASK)>>0)  //!< Get bbThreshold from bitmask config
#define UBX_CFG_ITFM_DATA0_CONFIG_CWTHRESHOLD_MASK 0x000001F0  //!< Mask for field cwThreshold in bitmask config
#define UBX_CFG_ITFM_DATA0_CONFIG_CWTHRESHOLD_GET(val)  (U)(((val)&UBX_CFG_ITFM_DATA0_CONFIG_CWTHRESHOLD_MASK)>>4)  //!< Get cwThreshold from bitmask config
#define UBX_CFG_ITFM_DATA0_CONFIG_ALGORITHMBITS_MASK 0x7FFFFE00  //!< Mask for field algorithmBits in bitmask config
#define UBX_CFG_ITFM_DATA0_CONFIG_ALGORITHMBITS_GET(val)  (U)(((val)&UBX_CFG_ITFM_DATA0_CONFIG_ALGORITHMBITS_MASK)>>9)  //!< Get algorithmBits from bitmask config
#define UBX_CFG_ITFM_DATA0_CONFIG_ENABLE_MASK 0x80000000  //!< Mask for field enable in bitmask config
#define UBX_CFG_ITFM_DATA0_CONFIG_ENABLE_GET(val)  (U)(((val)&UBX_CFG_ITFM_DATA0_CONFIG_ENABLE_MASK)>>31)  //!< Get enable from bitmask config

//@}
//! \name Bit Definitions for #UBX_CFG_ITFM_DATA0_s::config2
//@{
#define UBX_CFG_ITFM_DATA0_CONFIG2_GENERALBITS_MASK 0x00000FFF  //!< Mask for field generalBits in bitmask config2
#define UBX_CFG_ITFM_DATA0_CONFIG2_GENERALBITS_GET(val)  (U)(((val)&UBX_CFG_ITFM_DATA0_CONFIG2_GENERALBITS_MASK)>>0)  //!< Get generalBits from bitmask config2
#define UBX_CFG_ITFM_DATA0_CONFIG2_ANTSETTING_MASK 0x00003000  //!< Mask for field antSetting in bitmask config2
#define UBX_CFG_ITFM_DATA0_CONFIG2_ANTSETTING_GET(val)  (U)(((val)&UBX_CFG_ITFM_DATA0_CONFIG2_ANTSETTING_MASK)>>12)  //!< Get antSetting from bitmask config2
#define UBX_CFG_ITFM_DATA0_CONFIG2_ENABLE2_MASK 0x00004000  //!< Mask for field enable2 in bitmask config2
#define UBX_CFG_ITFM_DATA0_CONFIG2_ENABLE2_GET(val)  (U)(((val)&UBX_CFG_ITFM_DATA0_CONFIG2_ENABLE2_MASK)>>14)  //!< Get enable2 from bitmask config2

//@}


//#define UBXID_CFG_ITFM 0x0639  // already defined, see above


//================================================================
//! CFG_LOGFILTER_POLL0: Poll Request
/*!
Poll Data Logger filter Configuration
Upon sending of this message, the receiver returns CFG-LOGFILTER as defined below


This message's id is #UBXID_CFG_LOGFILTER
*/
//================================================================

typedef struct UBX_CFG_LOGFILTER_POLL0_s
{

} UBX_CFG_LOGFILTER_POLL0_t, *UBX_CFG_LOGFILTER_POLL0_pt;


#define UBXID_CFG_LOGFILTER 0x0647 //!< message id for CFG-LOGFILTER
	

//================================================================
//! CFG_LOGFILTER_DATA0: Input/Output
/*!
Data Logger Configuration
This message is used to enable/disable logging and to get or set the position entry filter settings.
Position entries can be filtered based on time difference, position difference or current speed thresholds. Position and speed filtering also have a minimum time interval.
A position is logged if any of the thresholds are exceeded. If a threshold is set to zero it is ignored. The maximum rate of position logging is 1Hz.
The filter settings will only be applied if the 'applyAllFilterSettings' flag is set. This enables recording to be enabled/disabled without affecting the other settings.


This message's id is #UBXID_CFG_LOGFILTER
*/
//================================================================

typedef struct UBX_CFG_LOGFILTER_DATA0_s
{
	U1  version;                  //!< The version of this message. Set to 1
	X1  flags;                    //!< Flags
	U2  minInterval;              //!< Minimum time interval between logged positions (0 = not set). <b>This is only applied in combination with the speed and/or position thresholds</b>
	U2  timeThreshold;            //!< If the time difference is greater than the threshold then the position is logged (0 = not set).
	U2  speedThreshold;           //!< If the current speed is greater than the threshold then the position is logged (0 = not set). minInterval also applies
	U4  positionThreshold;        //!< If the 3D position difference is greater than the threshold then the position is logged (0 = not set). minInterval also applies

} UBX_CFG_LOGFILTER_DATA0_t, *UBX_CFG_LOGFILTER_DATA0_pt;


//! \name Bit Definitions for #UBX_CFG_LOGFILTER_DATA0_s::flags
//@{
#define UBX_CFG_LOGFILTER_DATA0_FLAGS_RECORDENABLED_MASK 0x01  //!< Mask for field recordEnabled in bitmask flags
#define UBX_CFG_LOGFILTER_DATA0_FLAGS_RECORDENABLED_GET(val)  (U)(((val)&UBX_CFG_LOGFILTER_DATA0_FLAGS_RECORDENABLED_MASK)>>0)  //!< Get recordEnabled from bitmask flags
#define UBX_CFG_LOGFILTER_DATA0_FLAGS_PSMONCEPERWAKUPENABLED_MASK 0x02  //!< Mask for field psmOncePerWakupEnabled in bitmask flags
#define UBX_CFG_LOGFILTER_DATA0_FLAGS_PSMONCEPERWAKUPENABLED_GET(val)  (U)(((val)&UBX_CFG_LOGFILTER_DATA0_FLAGS_PSMONCEPERWAKUPENABLED_MASK)>>1)  //!< Get psmOncePerWakupEnabled from bitmask flags
#define UBX_CFG_LOGFILTER_DATA0_FLAGS_APPLYALLFILTERSETTINGS_MASK 0x04  //!< Mask for field applyAllFilterSettings in bitmask flags
#define UBX_CFG_LOGFILTER_DATA0_FLAGS_APPLYALLFILTERSETTINGS_GET(val)  (U)(((val)&UBX_CFG_LOGFILTER_DATA0_FLAGS_APPLYALLFILTERSETTINGS_MASK)>>2)  //!< Get applyAllFilterSettings from bitmask flags

//@}


//#define UBXID_CFG_LOGFILTER 0x0647  // already defined, see above


//================================================================
//! CFG_MSG_POLLID: Poll Request
/*!
Poll a message configuration
-


This message's id is #UBXID_CFG_MSG
*/
//================================================================

typedef struct UBX_CFG_MSG_POLLID_s
{
	U1  msgClass;                 //!< Message Class
	U1  msgID;                    //!< Message Identifier

} UBX_CFG_MSG_POLLID_t, *UBX_CFG_MSG_POLLID_pt;


#define UBXID_CFG_MSG 0x0601 //!< message id for CFG-MSG
	

//================================================================
//! CFG_MSG_SETU5: Input/Output
/*!
Set Message Rate(s)
Set/Get message rate configuration (s) to/from the receiver. See also section <r href=\"CFG-MSG-DESC'>How to change between protocols</r>.
* Send rate is relative to the event a message is registered on. For example, if the rate of a navigation message is set to 2, the message is sent every second navigation solution. For configuring NMEA messages, the section <r href=\"NMEA_ids'>NMEA Messages Overview</r> describes Class and Identifier numbers used.


This message's id is #UBXID_CFG_MSG
*/
//================================================================

typedef struct UBX_CFG_MSG_SETU5_s
{
	U1  msgClass;                 //!< Message Class
	U1  msgID;                    //!< Message Identifier
	U1  rate[6];                  //!< Send rate on I/O Port (6 Ports)

} UBX_CFG_MSG_SETU5_t, *UBX_CFG_MSG_SETU5_pt;


//#define UBXID_CFG_MSG 0x0601  // already defined, see above


//================================================================
//! CFG_MSG_SETCURRENT: Input/Output
/*!
Set Message Rate
Set message rate configuration for the current port. See also section <r href=\"CFG-MSG-DESC'>How to change between protocols</r>.


This message's id is #UBXID_CFG_MSG
*/
//================================================================

typedef struct UBX_CFG_MSG_SETCURRENT_s
{
	U1  msgClass;                 //!< Message Class
	U1  msgID;                    //!< Message Identifier
	U1  rate;                     //!< Send rate on current Port

} UBX_CFG_MSG_SETCURRENT_t, *UBX_CFG_MSG_SETCURRENT_pt;


//#define UBXID_CFG_MSG 0x0601  // already defined, see above


//================================================================
//! CFG_NAV5_POLL0: Poll Request
/*!
Poll Navigation Engine Settings
Sending this (empty / no-payload) message to the receiver results in the receiver returning a message of type CFG-NAV5 with a payload as defined below.


This message's id is #UBXID_CFG_NAV5
*/
//================================================================

typedef struct UBX_CFG_NAV5_POLL0_s
{

} UBX_CFG_NAV5_POLL0_t, *UBX_CFG_NAV5_POLL0_pt;


#define UBXID_CFG_NAV5 0x0624 //!< message id for CFG-NAV5
	

//================================================================
//! CFG_NAV5_DATA0: Input/Output
/*!
Navigation Engine Settings
See the <r href=\"CFG-NAV5-DESC'>Navigation Configuration Settings Description</r> for a detailed description of how these settings affect receiver operation.


This message's id is #UBXID_CFG_NAV5
*/
//================================================================

typedef struct UBX_CFG_NAV5_DATA0_s
{
	X2  mask;                     //!< Parameters Bitmask. Only the masked parameters will be applied.
	U1  dynModel;                 //!< Dynamic platform model:
	U1  fixMode;                  //!< Position Fixing Mode:
	I4  fixedAlt;                 //!< Fixed altitude (mean sea level) for 2D fix mode.
	U4  fixedAltVar;              //!< Fixed altitude variance for 2D mode.
	I1  minElev;                  //!< Minimum Elevation for a GNSS satellite to be used in NAV
	U1  drLimit;                  //!< Reserved
	U2  pDop;                     //!< Position DOP Mask to use
	U2  tDop;                     //!< Time DOP Mask to use
	U2  pAcc;                     //!< Position Accuracy Mask
	U2  tAcc;                     //!< Time Accuracy Mask
	U1  staticHoldThresh;         //!< Static hold threshold
	U1  dgpsTimeOut;              //!< DGPS timeout.
	U1  cnoThreshNumSVs;          //!< Number of satellites required to have C/N0 above cnoThresh for a fix to be attempted
	U1  cnoThresh;                //!< C/N0 threshold for deciding whether to attempt a fix
	U1  reserved1[2];             //!< <r href='DESC-UBX-Reserved'>Reserved</r>
	U2  staticHoldMaxDist;        //!< Static hold distance threshold (before quitting static hold)
	U1  utcStandard;              //!< UTC standard to be used:
	U1  reserved2[5];             //!< <r href='DESC-UBX-Reserved'>Reserved</r>

} UBX_CFG_NAV5_DATA0_t, *UBX_CFG_NAV5_DATA0_pt;


//! \name Bit Definitions for #UBX_CFG_NAV5_DATA0_s::mask
//@{
#define UBX_CFG_NAV5_DATA0_MASK_DYN_MASK 0x0001  //!< Mask for field dyn in bitmask mask
#define UBX_CFG_NAV5_DATA0_MASK_DYN_GET(val)  (U)(((val)&UBX_CFG_NAV5_DATA0_MASK_DYN_MASK)>>0)  //!< Get dyn from bitmask mask
#define UBX_CFG_NAV5_DATA0_MASK_MINEL_MASK 0x0002  //!< Mask for field minEl in bitmask mask
#define UBX_CFG_NAV5_DATA0_MASK_MINEL_GET(val)  (U)(((val)&UBX_CFG_NAV5_DATA0_MASK_MINEL_MASK)>>1)  //!< Get minEl from bitmask mask
#define UBX_CFG_NAV5_DATA0_MASK_POSFIXMODE_MASK 0x0004  //!< Mask for field posFixMode in bitmask mask
#define UBX_CFG_NAV5_DATA0_MASK_POSFIXMODE_GET(val)  (U)(((val)&UBX_CFG_NAV5_DATA0_MASK_POSFIXMODE_MASK)>>2)  //!< Get posFixMode from bitmask mask
#define UBX_CFG_NAV5_DATA0_MASK_DRLIM_MASK 0x0008  //!< Mask for field drLim in bitmask mask
#define UBX_CFG_NAV5_DATA0_MASK_DRLIM_GET(val)  (U)(((val)&UBX_CFG_NAV5_DATA0_MASK_DRLIM_MASK)>>3)  //!< Get drLim from bitmask mask
#define UBX_CFG_NAV5_DATA0_MASK_POSMASK_MASK 0x0010  //!< Mask for field posMask in bitmask mask
#define UBX_CFG_NAV5_DATA0_MASK_POSMASK_GET(val)  (U)(((val)&UBX_CFG_NAV5_DATA0_MASK_POSMASK_MASK)>>4)  //!< Get posMask from bitmask mask
#define UBX_CFG_NAV5_DATA0_MASK_TIMEMASK_MASK 0x0020  //!< Mask for field timeMask in bitmask mask
#define UBX_CFG_NAV5_DATA0_MASK_TIMEMASK_GET(val)  (U)(((val)&UBX_CFG_NAV5_DATA0_MASK_TIMEMASK_MASK)>>5)  //!< Get timeMask from bitmask mask
#define UBX_CFG_NAV5_DATA0_MASK_STATICHOLDMASK_MASK 0x0040  //!< Mask for field staticHoldMask in bitmask mask
#define UBX_CFG_NAV5_DATA0_MASK_STATICHOLDMASK_GET(val)  (U)(((val)&UBX_CFG_NAV5_DATA0_MASK_STATICHOLDMASK_MASK)>>6)  //!< Get staticHoldMask from bitmask mask
#define UBX_CFG_NAV5_DATA0_MASK_DGPSMASK_MASK 0x0080  //!< Mask for field dgpsMask in bitmask mask
#define UBX_CFG_NAV5_DATA0_MASK_DGPSMASK_GET(val)  (U)(((val)&UBX_CFG_NAV5_DATA0_MASK_DGPSMASK_MASK)>>7)  //!< Get dgpsMask from bitmask mask
#define UBX_CFG_NAV5_DATA0_MASK_CNOTHRESHOLD_MASK 0x0100  //!< Mask for field cnoThreshold in bitmask mask
#define UBX_CFG_NAV5_DATA0_MASK_CNOTHRESHOLD_GET(val)  (U)(((val)&UBX_CFG_NAV5_DATA0_MASK_CNOTHRESHOLD_MASK)>>8)  //!< Get cnoThreshold from bitmask mask
#define UBX_CFG_NAV5_DATA0_MASK_UTC_MASK 0x0400  //!< Mask for field utc in bitmask mask
#define UBX_CFG_NAV5_DATA0_MASK_UTC_GET(val)  (U)(((val)&UBX_CFG_NAV5_DATA0_MASK_UTC_MASK)>>10)  //!< Get utc from bitmask mask

//@}


//#define UBXID_CFG_NAV5 0x0624  // already defined, see above


//================================================================
//! CFG_NAVX5_POLL0: Poll Request
/*!
Poll Navigation Engine Expert Settings
Sending this (empty / no-payload) message to the receiver results in the receiver returning a message of type CFG-NAVX5 with a payload as defined below.


This message's id is #UBXID_CFG_NAVX5
*/
//================================================================

typedef struct UBX_CFG_NAVX5_POLL0_s
{

} UBX_CFG_NAVX5_POLL0_t, *UBX_CFG_NAVX5_POLL0_pt;


#define UBXID_CFG_NAVX5 0x0623 //!< message id for CFG-NAVX5
	

//================================================================
//! CFG_NAVX5_DATA0: Input/Output
/*!
Navigation Engine Expert Settings
-


This message's id is #UBXID_CFG_NAVX5
*/
//================================================================

typedef struct UBX_CFG_NAVX5_DATA0_s
{
	U2  version;                  //!< Message version (0 for this version)
	X2  mask1;                    //!< First parameters bitmask. Only the flagged parameters will be applied, unused bits must be set to 0.
	X4  mask2;                    //!< Second parameters bitmask. Only the flagged parameters will be applied, unused bits must be set to 0.
	U1  reserved1[2];             //!< <r href='DESC-UBX-Reserved'>Reserved</r>
	U1  minSVs;                   //!< Minimum number of satellites for navigation
	U1  maxSVs;                   //!< Maximum number of satellites for navigation
	U1  minCNO;                   //!< Minimum satellite signal level for navigation
	U1  reserved2;                //!< <r href='DESC-UBX-Reserved'>Reserved</r>
	U1  iniFix3D;                 //!< 1 = initial fix must be 3D
	U1  reserved3[2];             //!< <r href='DESC-UBX-Reserved'>Reserved</r>
	U1  ackAiding;                //!< 1 = issue acknowledgements for assistance message input
	U2  wknRollover;              //!< GPS week rollover number; GPS week numbers will be set correctly from this week up to 1024 weeks after this week. Setting this to 0 reverts to firmware default.
	U1  reserved4[6];             //!< <r href='DESC-UBX-Reserved'>Reserved</r>
	U1  usePPP;                   //!< 1 = use Precise Point Positioning (only available with the PPP product variant)
	U1  aopCfg;                   //!< <i>AssistNow Autonomous</i> configuration
	U1  reserved5[2];             //!< <r href='DESC-UBX-Reserved'>Reserved</r>
	U2  aopOrbMaxErr;             //!< Maximum acceptable (modeled) <i>AssistNow Autonomous</i> orbit error (valid range = 5..1000, or 0 = reset to firmware default)
	U1  reserved6[4];             //!< <r href='DESC-UBX-Reserved'>Reserved</r>
	U1  reserved7[3];             //!< <r href='DESC-UBX-Reserved'>Reserved</r>
	U1  useAdr;                   //!< <i>Only supported on certain product variants</i>

} UBX_CFG_NAVX5_DATA0_t, *UBX_CFG_NAVX5_DATA0_pt;


//! \name Bit Definitions for #UBX_CFG_NAVX5_DATA0_s::mask1
//@{
#define UBX_CFG_NAVX5_DATA0_MASK1_MINMAX_MASK 0x0004  //!< Mask for field minMax in bitmask mask1
#define UBX_CFG_NAVX5_DATA0_MASK1_MINMAX_GET(val)  (U)(((val)&UBX_CFG_NAVX5_DATA0_MASK1_MINMAX_MASK)>>2)  //!< Get minMax from bitmask mask1
#define UBX_CFG_NAVX5_DATA0_MASK1_MINCNO_MASK 0x0008  //!< Mask for field minCno in bitmask mask1
#define UBX_CFG_NAVX5_DATA0_MASK1_MINCNO_GET(val)  (U)(((val)&UBX_CFG_NAVX5_DATA0_MASK1_MINCNO_MASK)>>3)  //!< Get minCno from bitmask mask1
#define UBX_CFG_NAVX5_DATA0_MASK1_INITIAL3DFIX_MASK 0x0040  //!< Mask for field initial3dfix in bitmask mask1
#define UBX_CFG_NAVX5_DATA0_MASK1_INITIAL3DFIX_GET(val)  (U)(((val)&UBX_CFG_NAVX5_DATA0_MASK1_INITIAL3DFIX_MASK)>>6)  //!< Get initial3dfix from bitmask mask1
#define UBX_CFG_NAVX5_DATA0_MASK1_WKNROLL_MASK 0x0200  //!< Mask for field wknRoll in bitmask mask1
#define UBX_CFG_NAVX5_DATA0_MASK1_WKNROLL_GET(val)  (U)(((val)&UBX_CFG_NAVX5_DATA0_MASK1_WKNROLL_MASK)>>9)  //!< Get wknRoll from bitmask mask1
#define UBX_CFG_NAVX5_DATA0_MASK1_ACKAID_MASK 0x0400  //!< Mask for field ackAid in bitmask mask1
#define UBX_CFG_NAVX5_DATA0_MASK1_ACKAID_GET(val)  (U)(((val)&UBX_CFG_NAVX5_DATA0_MASK1_ACKAID_MASK)>>10)  //!< Get ackAid from bitmask mask1
#define UBX_CFG_NAVX5_DATA0_MASK1_PPP_MASK 0x2000  //!< Mask for field ppp in bitmask mask1
#define UBX_CFG_NAVX5_DATA0_MASK1_PPP_GET(val)  (U)(((val)&UBX_CFG_NAVX5_DATA0_MASK1_PPP_MASK)>>13)  //!< Get ppp from bitmask mask1
#define UBX_CFG_NAVX5_DATA0_MASK1_AOP_MASK 0x4000  //!< Mask for field aop in bitmask mask1
#define UBX_CFG_NAVX5_DATA0_MASK1_AOP_GET(val)  (U)(((val)&UBX_CFG_NAVX5_DATA0_MASK1_AOP_MASK)>>14)  //!< Get aop from bitmask mask1

//@}
//! \name Bit Definitions for #UBX_CFG_NAVX5_DATA0_s::mask2
//@{
#define UBX_CFG_NAVX5_DATA0_MASK2_ADR_MASK 0x00000040  //!< Mask for field adr in bitmask mask2
#define UBX_CFG_NAVX5_DATA0_MASK2_ADR_GET(val)  (U)(((val)&UBX_CFG_NAVX5_DATA0_MASK2_ADR_MASK)>>6)  //!< Get adr from bitmask mask2

//@}
//! \name Bit Definitions for #UBX_CFG_NAVX5_DATA0_s::aopCfg
//@{
#define UBX_CFG_NAVX5_DATA0_AOPCFG_USEAOP_MASK 0x01  //!< Mask for field useAOP in bitmask aopCfg
#define UBX_CFG_NAVX5_DATA0_AOPCFG_USEAOP_GET(val)  (U)(((val)&UBX_CFG_NAVX5_DATA0_AOPCFG_USEAOP_MASK)>>0)  //!< Get useAOP from bitmask aopCfg

//@}


//#define UBXID_CFG_NAVX5 0x0623  // already defined, see above


//================================================================
//! CFG_NMEA_POLL0: Poll Request
/*!
Poll the NMEA protocol configuration
-


This message's id is #UBXID_CFG_NMEA
*/
//================================================================

typedef struct UBX_CFG_NMEA_POLL0_s
{

} UBX_CFG_NMEA_POLL0_t, *UBX_CFG_NMEA_POLL0_pt;


#define UBXID_CFG_NMEA 0x0617 //!< message id for CFG-NMEA
	

//================================================================
//! CFG_NMEA_DATA0: Input/Output
/*!
NMEA protocol configuration (deprecated)
Set/Get the <r href=\"NMEA_overview'>NMEA protocol</r> configuration. See section <r href=\"CFG-NMEA-DESC'>NMEA Protocol Configuration</r> for a detailed description of the configuration effects on NMEA output.

   \note: This message version is provided for backwards compatibility only. Use the last version listed below instead (its fields are backwards compatible with this version, it just has extra fields defined).

This message's id is #UBXID_CFG_NMEA
*/
//================================================================

typedef struct UBX_CFG_NMEA_DATA0_s
{
	X1  filter;                   //!< filter flags
	U1  nmeaVersion;              //!< 0x23: NMEA version 2.3
	U1  numSV;                    //!< Maximum Number of SVs to report per TalkerId.
	X1  flags;                    //!< flags

} UBX_CFG_NMEA_DATA0_t, *UBX_CFG_NMEA_DATA0_pt;


//! \name Bit Definitions for #UBX_CFG_NMEA_DATA0_s::filter
//@{
#define UBX_CFG_NMEA_DATA0_FILTER_POSFILT_MASK 0x01  //!< Mask for field posFilt in bitmask filter
#define UBX_CFG_NMEA_DATA0_FILTER_POSFILT_GET(val)  (U)(((val)&UBX_CFG_NMEA_DATA0_FILTER_POSFILT_MASK)>>0)  //!< Get posFilt from bitmask filter
#define UBX_CFG_NMEA_DATA0_FILTER_MSKPOSFILT_MASK 0x02  //!< Mask for field mskPosFilt in bitmask filter
#define UBX_CFG_NMEA_DATA0_FILTER_MSKPOSFILT_GET(val)  (U)(((val)&UBX_CFG_NMEA_DATA0_FILTER_MSKPOSFILT_MASK)>>1)  //!< Get mskPosFilt from bitmask filter
#define UBX_CFG_NMEA_DATA0_FILTER_TIMEFILT_MASK 0x04  //!< Mask for field timeFilt in bitmask filter
#define UBX_CFG_NMEA_DATA0_FILTER_TIMEFILT_GET(val)  (U)(((val)&UBX_CFG_NMEA_DATA0_FILTER_TIMEFILT_MASK)>>2)  //!< Get timeFilt from bitmask filter
#define UBX_CFG_NMEA_DATA0_FILTER_DATEFILT_MASK 0x08  //!< Mask for field dateFilt in bitmask filter
#define UBX_CFG_NMEA_DATA0_FILTER_DATEFILT_GET(val)  (U)(((val)&UBX_CFG_NMEA_DATA0_FILTER_DATEFILT_MASK)>>3)  //!< Get dateFilt from bitmask filter
#define UBX_CFG_NMEA_DATA0_FILTER_GPSONLYFILTER_MASK 0x10  //!< Mask for field gpsOnlyFilter in bitmask filter
#define UBX_CFG_NMEA_DATA0_FILTER_GPSONLYFILTER_GET(val)  (U)(((val)&UBX_CFG_NMEA_DATA0_FILTER_GPSONLYFILTER_MASK)>>4)  //!< Get gpsOnlyFilter from bitmask filter
#define UBX_CFG_NMEA_DATA0_FILTER_TRACKFILT_MASK 0x20  //!< Mask for field trackFilt in bitmask filter
#define UBX_CFG_NMEA_DATA0_FILTER_TRACKFILT_GET(val)  (U)(((val)&UBX_CFG_NMEA_DATA0_FILTER_TRACKFILT_MASK)>>5)  //!< Get trackFilt from bitmask filter

//@}
//! \name Bit Definitions for #UBX_CFG_NMEA_DATA0_s::flags
//@{
#define UBX_CFG_NMEA_DATA0_FLAGS_COMPAT_MASK 0x01  //!< Mask for field compat in bitmask flags
#define UBX_CFG_NMEA_DATA0_FLAGS_COMPAT_GET(val)  (U)(((val)&UBX_CFG_NMEA_DATA0_FLAGS_COMPAT_MASK)>>0)  //!< Get compat from bitmask flags
#define UBX_CFG_NMEA_DATA0_FLAGS_CONSIDER_MASK 0x02  //!< Mask for field consider in bitmask flags
#define UBX_CFG_NMEA_DATA0_FLAGS_CONSIDER_GET(val)  (U)(((val)&UBX_CFG_NMEA_DATA0_FLAGS_CONSIDER_MASK)>>1)  //!< Get consider from bitmask flags

//@}


//#define UBXID_CFG_NMEA 0x0617  // already defined, see above


//================================================================
//! CFG_NMEA_DATA1: Input/Output
/*!
NMEA protocol configuration V0 (deprecated)
Set/Get the <r href=\"NMEA_overview'>NMEA protocol</r> configuration. See section <r href=\"CFG-NMEA-DESC'>NMEA Protocol Configuration</r> for a detailed description of the configuration effects on NMEA output.

   \note: This message version is provided for backwards compatibility only. Use the last version listed below instead (its fields are backwards compatible with this version, it just has extra fields defined).

This message's id is #UBXID_CFG_NMEA
*/
//================================================================

typedef struct UBX_CFG_NMEA_DATA1_s
{
	X1  filter;                   //!< filter flags
	U1  nmeaVersion;              //!< 0x23: NMEA version 2.3
	U1  numSV;                    //!< Maximum Number of SVs to report per TalkerId.
	X1  flags;                    //!< flags
	X4  gnssToFilter;             //!< Filters out satellites based on their GNSS. If a bitfield is enabled, the corresponding satellites will be not output.
	U1  svNumbering;              //!< Configures the display of satellites that do not have an NMEA-defined value.
	U1  mainTalkerId;             //!< By default the main Talker ID (i.e. the Talker ID used for all messages other than GSV) is determined by the GNSS assignment of the receiver's channels (see <rc href=\"UBX-CFG-GNSS'>UBX-CFG-GNSS</rc>).
	U1  gsvTalkerId;              //!< By default the Talker ID for GSV messages is GNSS specific (as defined by NMEA).
	U1  version;                  //!< Message version (set to 0 for this version)

} UBX_CFG_NMEA_DATA1_t, *UBX_CFG_NMEA_DATA1_pt;


//! \name Bit Definitions for #UBX_CFG_NMEA_DATA1_s::filter
//@{
#define UBX_CFG_NMEA_DATA1_FILTER_POSFILT_MASK 0x01  //!< Mask for field posFilt in bitmask filter
#define UBX_CFG_NMEA_DATA1_FILTER_POSFILT_GET(val)  (U)(((val)&UBX_CFG_NMEA_DATA1_FILTER_POSFILT_MASK)>>0)  //!< Get posFilt from bitmask filter
#define UBX_CFG_NMEA_DATA1_FILTER_MSKPOSFILT_MASK 0x02  //!< Mask for field mskPosFilt in bitmask filter
#define UBX_CFG_NMEA_DATA1_FILTER_MSKPOSFILT_GET(val)  (U)(((val)&UBX_CFG_NMEA_DATA1_FILTER_MSKPOSFILT_MASK)>>1)  //!< Get mskPosFilt from bitmask filter
#define UBX_CFG_NMEA_DATA1_FILTER_TIMEFILT_MASK 0x04  //!< Mask for field timeFilt in bitmask filter
#define UBX_CFG_NMEA_DATA1_FILTER_TIMEFILT_GET(val)  (U)(((val)&UBX_CFG_NMEA_DATA1_FILTER_TIMEFILT_MASK)>>2)  //!< Get timeFilt from bitmask filter
#define UBX_CFG_NMEA_DATA1_FILTER_DATEFILT_MASK 0x08  //!< Mask for field dateFilt in bitmask filter
#define UBX_CFG_NMEA_DATA1_FILTER_DATEFILT_GET(val)  (U)(((val)&UBX_CFG_NMEA_DATA1_FILTER_DATEFILT_MASK)>>3)  //!< Get dateFilt from bitmask filter
#define UBX_CFG_NMEA_DATA1_FILTER_GPSONLYFILTER_MASK 0x10  //!< Mask for field gpsOnlyFilter in bitmask filter
#define UBX_CFG_NMEA_DATA1_FILTER_GPSONLYFILTER_GET(val)  (U)(((val)&UBX_CFG_NMEA_DATA1_FILTER_GPSONLYFILTER_MASK)>>4)  //!< Get gpsOnlyFilter from bitmask filter
#define UBX_CFG_NMEA_DATA1_FILTER_TRACKFILT_MASK 0x20  //!< Mask for field trackFilt in bitmask filter
#define UBX_CFG_NMEA_DATA1_FILTER_TRACKFILT_GET(val)  (U)(((val)&UBX_CFG_NMEA_DATA1_FILTER_TRACKFILT_MASK)>>5)  //!< Get trackFilt from bitmask filter

//@}
//! \name Bit Definitions for #UBX_CFG_NMEA_DATA1_s::flags
//@{
#define UBX_CFG_NMEA_DATA1_FLAGS_COMPAT_MASK 0x01  //!< Mask for field compat in bitmask flags
#define UBX_CFG_NMEA_DATA1_FLAGS_COMPAT_GET(val)  (U)(((val)&UBX_CFG_NMEA_DATA1_FLAGS_COMPAT_MASK)>>0)  //!< Get compat from bitmask flags
#define UBX_CFG_NMEA_DATA1_FLAGS_CONSIDER_MASK 0x02  //!< Mask for field consider in bitmask flags
#define UBX_CFG_NMEA_DATA1_FLAGS_CONSIDER_GET(val)  (U)(((val)&UBX_CFG_NMEA_DATA1_FLAGS_CONSIDER_MASK)>>1)  //!< Get consider from bitmask flags

//@}
//! \name Bit Definitions for #UBX_CFG_NMEA_DATA1_s::gnssToFilter
//@{
#define UBX_CFG_NMEA_DATA1_GNSSTOFILTER_GPS_MASK 0x01  //!< Mask for field gps in bitmask gnssToFilter
#define UBX_CFG_NMEA_DATA1_GNSSTOFILTER_GPS_GET(val)  (U)(((val)&UBX_CFG_NMEA_DATA1_GNSSTOFILTER_GPS_MASK)>>0)  //!< Get gps from bitmask gnssToFilter
#define UBX_CFG_NMEA_DATA1_GNSSTOFILTER_SBAS_MASK 0x02  //!< Mask for field sbas in bitmask gnssToFilter
#define UBX_CFG_NMEA_DATA1_GNSSTOFILTER_SBAS_GET(val)  (U)(((val)&UBX_CFG_NMEA_DATA1_GNSSTOFILTER_SBAS_MASK)>>1)  //!< Get sbas from bitmask gnssToFilter
#define UBX_CFG_NMEA_DATA1_GNSSTOFILTER_QZSS_MASK 0x10  //!< Mask for field qzss in bitmask gnssToFilter
#define UBX_CFG_NMEA_DATA1_GNSSTOFILTER_QZSS_GET(val)  (U)(((val)&UBX_CFG_NMEA_DATA1_GNSSTOFILTER_QZSS_MASK)>>4)  //!< Get qzss from bitmask gnssToFilter
#define UBX_CFG_NMEA_DATA1_GNSSTOFILTER_GLONASS_MASK 0x20  //!< Mask for field glonass in bitmask gnssToFilter
#define UBX_CFG_NMEA_DATA1_GNSSTOFILTER_GLONASS_GET(val)  (U)(((val)&UBX_CFG_NMEA_DATA1_GNSSTOFILTER_GLONASS_MASK)>>5)  //!< Get glonass from bitmask gnssToFilter
#define UBX_CFG_NMEA_DATA1_GNSSTOFILTER_BEIDOU_MASK 0x40  //!< Mask for field beidou in bitmask gnssToFilter
#define UBX_CFG_NMEA_DATA1_GNSSTOFILTER_BEIDOU_GET(val)  (U)(((val)&UBX_CFG_NMEA_DATA1_GNSSTOFILTER_BEIDOU_MASK)>>6)  //!< Get beidou from bitmask gnssToFilter

//@}


//#define UBXID_CFG_NMEA 0x0617  // already defined, see above


//================================================================
//! CFG_NMEA_DATA2: Input/Output
/*!
Extended NMEA protocol configuration V1
Set/Get the <r href=\"NMEA_overview'>NMEA protocol</r> configuration. See section <r href=\"CFG-NMEA-DESC'>NMEA Protocol Configuration</r> for a detailed description of the configuration effects on NMEA output.


This message's id is #UBXID_CFG_NMEA
*/
//================================================================

typedef struct UBX_CFG_NMEA_DATA2_s
{
	X1  filter;                   //!< filter flags
	U1  nmeaVersion;              //!< 0x41: NMEA version 4.1
	U1  numSV;                    //!< Maximum Number of SVs to report per TalkerId.
	X1  flags;                    //!< flags
	X4  gnssToFilter;             //!< Filters out satellites based on their GNSS. If a bitfield is enabled, the corresponding satellites will be not output.
	U1  svNumbering;              //!< Configures the display of satellites that do not have an NMEA-defined value.
	U1  mainTalkerId;             //!< By default the main Talker ID (i.e. the Talker ID used for all messages other than GSV) is determined by the GNSS assignment of the receiver's channels (see <rc href=\"UBX-CFG-GNSS'>UBX-CFG-GNSS</rc>).
	U1  gsvTalkerId;              //!< By default the Talker ID for GSV messages is GNSS specific (as defined by NMEA).
	U1  version;                  //!< Message version (set to 1 for this version)
	CH  bdsTalkerId[2];           //!< Sets the two characters that should be used for the BeiDou Talker ID
	U1  reserved1[6];             //!< <r href='DESC-UBX-Reserved'>Reserved</r>

} UBX_CFG_NMEA_DATA2_t, *UBX_CFG_NMEA_DATA2_pt;


//! \name Bit Definitions for #UBX_CFG_NMEA_DATA2_s::filter
//@{
#define UBX_CFG_NMEA_DATA2_FILTER_POSFILT_MASK 0x01  //!< Mask for field posFilt in bitmask filter
#define UBX_CFG_NMEA_DATA2_FILTER_POSFILT_GET(val)  (U)(((val)&UBX_CFG_NMEA_DATA2_FILTER_POSFILT_MASK)>>0)  //!< Get posFilt from bitmask filter
#define UBX_CFG_NMEA_DATA2_FILTER_MSKPOSFILT_MASK 0x02  //!< Mask for field mskPosFilt in bitmask filter
#define UBX_CFG_NMEA_DATA2_FILTER_MSKPOSFILT_GET(val)  (U)(((val)&UBX_CFG_NMEA_DATA2_FILTER_MSKPOSFILT_MASK)>>1)  //!< Get mskPosFilt from bitmask filter
#define UBX_CFG_NMEA_DATA2_FILTER_TIMEFILT_MASK 0x04  //!< Mask for field timeFilt in bitmask filter
#define UBX_CFG_NMEA_DATA2_FILTER_TIMEFILT_GET(val)  (U)(((val)&UBX_CFG_NMEA_DATA2_FILTER_TIMEFILT_MASK)>>2)  //!< Get timeFilt from bitmask filter
#define UBX_CFG_NMEA_DATA2_FILTER_DATEFILT_MASK 0x08  //!< Mask for field dateFilt in bitmask filter
#define UBX_CFG_NMEA_DATA2_FILTER_DATEFILT_GET(val)  (U)(((val)&UBX_CFG_NMEA_DATA2_FILTER_DATEFILT_MASK)>>3)  //!< Get dateFilt from bitmask filter
#define UBX_CFG_NMEA_DATA2_FILTER_GPSONLYFILTER_MASK 0x10  //!< Mask for field gpsOnlyFilter in bitmask filter
#define UBX_CFG_NMEA_DATA2_FILTER_GPSONLYFILTER_GET(val)  (U)(((val)&UBX_CFG_NMEA_DATA2_FILTER_GPSONLYFILTER_MASK)>>4)  //!< Get gpsOnlyFilter from bitmask filter
#define UBX_CFG_NMEA_DATA2_FILTER_TRACKFILT_MASK 0x20  //!< Mask for field trackFilt in bitmask filter
#define UBX_CFG_NMEA_DATA2_FILTER_TRACKFILT_GET(val)  (U)(((val)&UBX_CFG_NMEA_DATA2_FILTER_TRACKFILT_MASK)>>5)  //!< Get trackFilt from bitmask filter

//@}
//! \name Bit Definitions for #UBX_CFG_NMEA_DATA2_s::flags
//@{
#define UBX_CFG_NMEA_DATA2_FLAGS_COMPAT_MASK 0x01  //!< Mask for field compat in bitmask flags
#define UBX_CFG_NMEA_DATA2_FLAGS_COMPAT_GET(val)  (U)(((val)&UBX_CFG_NMEA_DATA2_FLAGS_COMPAT_MASK)>>0)  //!< Get compat from bitmask flags
#define UBX_CFG_NMEA_DATA2_FLAGS_CONSIDER_MASK 0x02  //!< Mask for field consider in bitmask flags
#define UBX_CFG_NMEA_DATA2_FLAGS_CONSIDER_GET(val)  (U)(((val)&UBX_CFG_NMEA_DATA2_FLAGS_CONSIDER_MASK)>>1)  //!< Get consider from bitmask flags
#define UBX_CFG_NMEA_DATA2_FLAGS_LIMIT82_MASK 0x04  //!< Mask for field limit82 in bitmask flags
#define UBX_CFG_NMEA_DATA2_FLAGS_LIMIT82_GET(val)  (U)(((val)&UBX_CFG_NMEA_DATA2_FLAGS_LIMIT82_MASK)>>2)  //!< Get limit82 from bitmask flags

//@}
//! \name Bit Definitions for #UBX_CFG_NMEA_DATA2_s::gnssToFilter
//@{
#define UBX_CFG_NMEA_DATA2_GNSSTOFILTER_GPS_MASK 0x01  //!< Mask for field gps in bitmask gnssToFilter
#define UBX_CFG_NMEA_DATA2_GNSSTOFILTER_GPS_GET(val)  (U)(((val)&UBX_CFG_NMEA_DATA2_GNSSTOFILTER_GPS_MASK)>>0)  //!< Get gps from bitmask gnssToFilter
#define UBX_CFG_NMEA_DATA2_GNSSTOFILTER_SBAS_MASK 0x02  //!< Mask for field sbas in bitmask gnssToFilter
#define UBX_CFG_NMEA_DATA2_GNSSTOFILTER_SBAS_GET(val)  (U)(((val)&UBX_CFG_NMEA_DATA2_GNSSTOFILTER_SBAS_MASK)>>1)  //!< Get sbas from bitmask gnssToFilter
#define UBX_CFG_NMEA_DATA2_GNSSTOFILTER_QZSS_MASK 0x10  //!< Mask for field qzss in bitmask gnssToFilter
#define UBX_CFG_NMEA_DATA2_GNSSTOFILTER_QZSS_GET(val)  (U)(((val)&UBX_CFG_NMEA_DATA2_GNSSTOFILTER_QZSS_MASK)>>4)  //!< Get qzss from bitmask gnssToFilter
#define UBX_CFG_NMEA_DATA2_GNSSTOFILTER_GLONASS_MASK 0x20  //!< Mask for field glonass in bitmask gnssToFilter
#define UBX_CFG_NMEA_DATA2_GNSSTOFILTER_GLONASS_GET(val)  (U)(((val)&UBX_CFG_NMEA_DATA2_GNSSTOFILTER_GLONASS_MASK)>>5)  //!< Get glonass from bitmask gnssToFilter
#define UBX_CFG_NMEA_DATA2_GNSSTOFILTER_BEIDOU_MASK 0x40  //!< Mask for field beidou in bitmask gnssToFilter
#define UBX_CFG_NMEA_DATA2_GNSSTOFILTER_BEIDOU_GET(val)  (U)(((val)&UBX_CFG_NMEA_DATA2_GNSSTOFILTER_BEIDOU_MASK)>>6)  //!< Get beidou from bitmask gnssToFilter

//@}


//#define UBXID_CFG_NMEA 0x0617  // already defined, see above


//================================================================
//! CFG_ODO_POLL1: Poll Request
/*!
Poll Odometer, Low-speed COG Engine Settings
Sending this (empty / no-payload) message to the receiver results in the receiver returning a message of type CFG-ODO with a payload as defined below.


This message's id is #UBXID_CFG_ODO
*/
//================================================================

typedef struct UBX_CFG_ODO_POLL1_s
{

} UBX_CFG_ODO_POLL1_t, *UBX_CFG_ODO_POLL1_pt;


#define UBXID_CFG_ODO 0x061E //!< message id for CFG-ODO
	

//================================================================
//! CFG_ODO_DATA1: Input/Output
/*!
Odometer, Low-speed COG Engine Settings
-

   \note: This feature is not supported for the FTS product variant.

This message's id is #UBXID_CFG_ODO
*/
//================================================================

typedef struct UBX_CFG_ODO_DATA1_s
{
	U1  version;                  //!< Message version (0 for this version)
	U1  reserved1[3];             //!< <r href='DESC-UBX-Reserved'>Reserved</r>
	U1  flags;                    //!< <i>Odometer/Low-speed COG filter</i> flags
	X1  odoCfg;                   //!< <i>Odometer filter</i> settings
	U1  reserved2[6];             //!< <r href='DESC-UBX-Reserved'>Reserved</r>
	U1  cogMaxSpeed;              //!< Speed below which course-over-ground (COG) is computed with the low-speed COG filter
	U1  cogMaxPosAcc;             //!< Maximum acceptable position accuracy for computing COG with the low-speed COG filter
	U1  reserved3[2];             //!< <r href='DESC-UBX-Reserved'>Reserved</r>
	U1  velLpGain;                //!< Velocity low-pass filter level, range 0..255
	U1  cogLpGain;                //!< COG low-pass filter level (at speed < 8 m/s), range 0..255
	U1  reserved4[2];             //!< <r href='DESC-UBX-Reserved'>Reserved</r>

} UBX_CFG_ODO_DATA1_t, *UBX_CFG_ODO_DATA1_pt;


//! \name Bit Definitions for #UBX_CFG_ODO_DATA1_s::flags
//@{
#define UBX_CFG_ODO_DATA1_FLAGS_USEODO_MASK 0x01  //!< Mask for field useODO in bitmask flags
#define UBX_CFG_ODO_DATA1_FLAGS_USEODO_GET(val)  (U)(((val)&UBX_CFG_ODO_DATA1_FLAGS_USEODO_MASK)>>0)  //!< Get useODO from bitmask flags
#define UBX_CFG_ODO_DATA1_FLAGS_USECOG_MASK 0x02  //!< Mask for field useCOG in bitmask flags
#define UBX_CFG_ODO_DATA1_FLAGS_USECOG_GET(val)  (U)(((val)&UBX_CFG_ODO_DATA1_FLAGS_USECOG_MASK)>>1)  //!< Get useCOG from bitmask flags
#define UBX_CFG_ODO_DATA1_FLAGS_OUTLPVEL_MASK 0x04  //!< Mask for field outLPVel in bitmask flags
#define UBX_CFG_ODO_DATA1_FLAGS_OUTLPVEL_GET(val)  (U)(((val)&UBX_CFG_ODO_DATA1_FLAGS_OUTLPVEL_MASK)>>2)  //!< Get outLPVel from bitmask flags
#define UBX_CFG_ODO_DATA1_FLAGS_OUTLPCOG_MASK 0x08  //!< Mask for field outLPCog in bitmask flags
#define UBX_CFG_ODO_DATA1_FLAGS_OUTLPCOG_GET(val)  (U)(((val)&UBX_CFG_ODO_DATA1_FLAGS_OUTLPCOG_MASK)>>3)  //!< Get outLPCog from bitmask flags

//@}
//! \name Bit Definitions for #UBX_CFG_ODO_DATA1_s::odoCfg
//@{
#define UBX_CFG_ODO_DATA1_ODOCFG_PROFILE_MASK 0x07  //!< Mask for field profile in bitmask odoCfg
#define UBX_CFG_ODO_DATA1_ODOCFG_PROFILE_GET(val)  (U)(((val)&UBX_CFG_ODO_DATA1_ODOCFG_PROFILE_MASK)>>0)  //!< Get profile from bitmask odoCfg

//@}


//#define UBXID_CFG_ODO 0x061E  // already defined, see above


//================================================================
//! CFG_PM2_POLL0: Poll Request
/*!
Poll extended Power Mgmt configuration
-


This message's id is #UBXID_CFG_PM2
*/
//================================================================

typedef struct UBX_CFG_PM2_POLL0_s
{

} UBX_CFG_PM2_POLL0_t, *UBX_CFG_PM2_POLL0_pt;


#define UBXID_CFG_PM2 0x063B //!< message id for CFG-PM2
	

//================================================================
//! CFG_PM2_DATA0: Input/Output
/*!
Extended Power Management configuration
-

   \note: This feature is not supported for either the ADR or FTS product variants.

This message's id is #UBXID_CFG_PM2
*/
//================================================================

typedef struct UBX_CFG_PM2_DATA0_s
{
	U1  version;                  //!< Message version (1 for this version)
	U1  reserved1;                //!< <r href='DESC-UBX-Reserved'>Reserved</r>
	U1  maxStartupStateDur;       //!< Maximum time to spend in <i>Acquisition</i> state. If 0: bound disabled (see <r href=\"PM-DESC-MAXSTARTUPSTATEDUR'>maxStartupStateDur</r>). (Only supported in <r href='ProtocolVersions'>protocol versions 17+</r>)
	U1  reserved2;                //!< <r href='DESC-UBX-Reserved'>Reserved</r>
	X4  flags;                    //!< PSM configuration flags
	U4  updatePeriod;             //!< Position update period. If set to 0, the receiver will never retry a fix and it will wait for external events
	U4  searchPeriod;             //!< Acquisition retry period if previously failed. If set to 0, the receiver will never retry a startup
	U4  gridOffset;               //!< Grid offset relative to GPS start of week
	U2  onTime;                   //!< Time to stay in <i>Tracking</i> state
	U2  minAcqTime;               //!< minimal search time
	U1  reserved3[20];            //!< <r href='DESC-UBX-Reserved'>Reserved</r>

} UBX_CFG_PM2_DATA0_t, *UBX_CFG_PM2_DATA0_pt;


//! \name Bit Definitions for #UBX_CFG_PM2_DATA0_s::flags
//@{
#define UBX_CFG_PM2_DATA0_FLAGS_EXTINTSEL_MASK 0x00000010  //!< Mask for field extintSel in bitmask flags
#define UBX_CFG_PM2_DATA0_FLAGS_EXTINTSEL_GET(val)  (U)(((val)&UBX_CFG_PM2_DATA0_FLAGS_EXTINTSEL_MASK)>>4)  //!< Get extintSel from bitmask flags
#define UBX_CFG_PM2_DATA0_FLAGS_EXTINTWAKE_MASK 0x00000020  //!< Mask for field extintWake in bitmask flags
#define UBX_CFG_PM2_DATA0_FLAGS_EXTINTWAKE_GET(val)  (U)(((val)&UBX_CFG_PM2_DATA0_FLAGS_EXTINTWAKE_MASK)>>5)  //!< Get extintWake from bitmask flags
#define UBX_CFG_PM2_DATA0_FLAGS_EXTINTBACKUP_MASK 0x00000040  //!< Mask for field extintBackup in bitmask flags
#define UBX_CFG_PM2_DATA0_FLAGS_EXTINTBACKUP_GET(val)  (U)(((val)&UBX_CFG_PM2_DATA0_FLAGS_EXTINTBACKUP_MASK)>>6)  //!< Get extintBackup from bitmask flags
#define UBX_CFG_PM2_DATA0_FLAGS_LIMITPEAKCURR_MASK 0x00000300  //!< Mask for field limitPeakCurr in bitmask flags
#define UBX_CFG_PM2_DATA0_FLAGS_LIMITPEAKCURR_GET(val)  (U)(((val)&UBX_CFG_PM2_DATA0_FLAGS_LIMITPEAKCURR_MASK)>>8)  //!< Get limitPeakCurr from bitmask flags
#define UBX_CFG_PM2_DATA0_FLAGS_WAITTIMEFIX_MASK 0x00000400  //!< Mask for field waitTimeFix in bitmask flags
#define UBX_CFG_PM2_DATA0_FLAGS_WAITTIMEFIX_GET(val)  (U)(((val)&UBX_CFG_PM2_DATA0_FLAGS_WAITTIMEFIX_MASK)>>10)  //!< Get waitTimeFix from bitmask flags
#define UBX_CFG_PM2_DATA0_FLAGS_UPDATERTC_MASK 0x00000800  //!< Mask for field updateRTC in bitmask flags
#define UBX_CFG_PM2_DATA0_FLAGS_UPDATERTC_GET(val)  (U)(((val)&UBX_CFG_PM2_DATA0_FLAGS_UPDATERTC_MASK)>>11)  //!< Get updateRTC from bitmask flags
#define UBX_CFG_PM2_DATA0_FLAGS_UPDATEEPH_MASK 0x00001000  //!< Mask for field updateEPH in bitmask flags
#define UBX_CFG_PM2_DATA0_FLAGS_UPDATEEPH_GET(val)  (U)(((val)&UBX_CFG_PM2_DATA0_FLAGS_UPDATEEPH_MASK)>>12)  //!< Get updateEPH from bitmask flags
#define UBX_CFG_PM2_DATA0_FLAGS_DONOTENTEROFF_MASK 0x00010000  //!< Mask for field doNotEnterOff in bitmask flags
#define UBX_CFG_PM2_DATA0_FLAGS_DONOTENTEROFF_GET(val)  (U)(((val)&UBX_CFG_PM2_DATA0_FLAGS_DONOTENTEROFF_MASK)>>16)  //!< Get doNotEnterOff from bitmask flags
#define UBX_CFG_PM2_DATA0_FLAGS_MODE_MASK 0x00060000  //!< Mask for field mode in bitmask flags
#define UBX_CFG_PM2_DATA0_FLAGS_MODE_GET(val)  (U)(((val)&UBX_CFG_PM2_DATA0_FLAGS_MODE_MASK)>>17)  //!< Get mode from bitmask flags

//@}


//#define UBXID_CFG_PM2 0x063B  // already defined, see above


//================================================================
//! CFG_PRT_POLL0: Poll Request
/*!
Polls the configuration of the used I/O Port
Polls the configuration of the I/O Port on which this message is received


This message's id is #UBXID_CFG_PRT
*/
//================================================================

typedef struct UBX_CFG_PRT_POLL0_s
{

} UBX_CFG_PRT_POLL0_t, *UBX_CFG_PRT_POLL0_pt;


#define UBXID_CFG_PRT 0x0600 //!< message id for CFG-PRT
	

//================================================================
//! CFG_PRT_POLLID: Poll Request
/*!
Polls the configuration for one I/O Port
Sending this message with a port ID as payload results in having the receiver return the configuration for the specified port.


This message's id is #UBXID_CFG_PRT
*/
//================================================================

typedef struct UBX_CFG_PRT_POLLID_s
{
	U1  PortID;                   //!< Port Identifier Number (see the other versions of CFG-PRT for valid values)

} UBX_CFG_PRT_POLLID_t, *UBX_CFG_PRT_POLLID_pt;


//#define UBXID_CFG_PRT 0x0600  // already defined, see above


//================================================================
//! CFG_PRT_UART: Input/Output
/*!
Port Configuration for UART
Several configurations can be concatenated to one input message. In this case the payload length can be a multiple of the normal length (see the other versions of CFG-PRT). Output messages from the module contain only one configuration unit.
Note that this message can affect baud rate and other transmission parameters. Because there may be messages queued for transmission there may be uncertainty about which protocol applies to such messages. In addition a message currently in transmission may be corrupted by a protocol change. Host data reception paramaters may have to be changed to be able to receive future messages, including the acknowledge message resulting from the CFG-PRT message.


This message's id is #UBXID_CFG_PRT
*/
//================================================================

typedef struct UBX_CFG_PRT_UART_s
{
	U1  portID;                   //!< Port Identifier Number (see <r href=\"CFG-PRT-DESC'>Serial Communication Ports Description</r> for valid UART port IDs)
	U1  reserved1;                //!< <r href='DESC-UBX-Reserved'>Reserved</r>
	X2  txReady;                  //!< TX ready PIN configuration
	X4  mode;                     //!< A bit mask describing the UART mode
	U4  baudRate;                 //!< Baud rate in bits/second
	X2  inProtoMask;              //!< A mask describing which input protocols are active.
	X2  outProtoMask;             //!< A mask describing which output protocols are active.
	X2  flags;                    //!< Flags bit mask
	U1  reserved2[2];             //!< <r href='DESC-UBX-Reserved'>Reserved</r>

} UBX_CFG_PRT_UART_t, *UBX_CFG_PRT_UART_pt;


//! \name Bit Definitions for #UBX_CFG_PRT_UART_s::txReady
//@{
#define UBX_CFG_PRT_UART_TXREADY_EN_MASK 0x00000001  //!< Mask for field en in bitmask txReady
#define UBX_CFG_PRT_UART_TXREADY_EN_GET(val)  (U)(((val)&UBX_CFG_PRT_UART_TXREADY_EN_MASK)>>0)  //!< Get en from bitmask txReady
#define UBX_CFG_PRT_UART_TXREADY_POL_MASK 0x00000002  //!< Mask for field pol in bitmask txReady
#define UBX_CFG_PRT_UART_TXREADY_POL_GET(val)  (U)(((val)&UBX_CFG_PRT_UART_TXREADY_POL_MASK)>>1)  //!< Get pol from bitmask txReady
#define UBX_CFG_PRT_UART_TXREADY_PIN_MASK 0x0000007C  //!< Mask for field pin in bitmask txReady
#define UBX_CFG_PRT_UART_TXREADY_PIN_GET(val)  (U)(((val)&UBX_CFG_PRT_UART_TXREADY_PIN_MASK)>>2)  //!< Get pin from bitmask txReady
#define UBX_CFG_PRT_UART_TXREADY_THRES_MASK 0x0000FF80  //!< Mask for field thres in bitmask txReady
#define UBX_CFG_PRT_UART_TXREADY_THRES_GET(val)  (U)(((val)&UBX_CFG_PRT_UART_TXREADY_THRES_MASK)>>7)  //!< Get thres from bitmask txReady

//@}
//! \name Bit Definitions for #UBX_CFG_PRT_UART_s::mode
//@{
#define UBX_CFG_PRT_UART_MODE_CHARLEN_MASK 0x000000C0  //!< Mask for field charLen in bitmask mode
#define UBX_CFG_PRT_UART_MODE_CHARLEN_GET(val)  (U)(((val)&UBX_CFG_PRT_UART_MODE_CHARLEN_MASK)>>6)  //!< Get charLen from bitmask mode
#define UBX_CFG_PRT_UART_MODE_PARITY_MASK 0x00000E00  //!< Mask for field parity in bitmask mode
#define UBX_CFG_PRT_UART_MODE_PARITY_GET(val)  (U)(((val)&UBX_CFG_PRT_UART_MODE_PARITY_MASK)>>9)  //!< Get parity from bitmask mode
#define UBX_CFG_PRT_UART_MODE_NSTOPBITS_MASK 0x00003000  //!< Mask for field nStopBits in bitmask mode
#define UBX_CFG_PRT_UART_MODE_NSTOPBITS_GET(val)  (U)(((val)&UBX_CFG_PRT_UART_MODE_NSTOPBITS_MASK)>>12)  //!< Get nStopBits from bitmask mode

//@}
//! \name Bit Definitions for #UBX_CFG_PRT_UART_s::inProtoMask
//@{
#define UBX_CFG_PRT_UART_INPROTOMASK_INUBX_MASK 0x0001  //!< Mask for field inUbx in bitmask inProtoMask
#define UBX_CFG_PRT_UART_INPROTOMASK_INUBX_GET(val)  (U)(((val)&UBX_CFG_PRT_UART_INPROTOMASK_INUBX_MASK)>>0)  //!< Get inUbx from bitmask inProtoMask
#define UBX_CFG_PRT_UART_INPROTOMASK_INNMEA_MASK 0x0002  //!< Mask for field inNmea in bitmask inProtoMask
#define UBX_CFG_PRT_UART_INPROTOMASK_INNMEA_GET(val)  (U)(((val)&UBX_CFG_PRT_UART_INPROTOMASK_INNMEA_MASK)>>1)  //!< Get inNmea from bitmask inProtoMask
#define UBX_CFG_PRT_UART_INPROTOMASK_INRTCM_MASK 0x0004  //!< Mask for field inRtcm in bitmask inProtoMask
#define UBX_CFG_PRT_UART_INPROTOMASK_INRTCM_GET(val)  (U)(((val)&UBX_CFG_PRT_UART_INPROTOMASK_INRTCM_MASK)>>2)  //!< Get inRtcm from bitmask inProtoMask

//@}
//! \name Bit Definitions for #UBX_CFG_PRT_UART_s::outProtoMask
//@{
#define UBX_CFG_PRT_UART_OUTPROTOMASK_OUTUBX_MASK 0x0001  //!< Mask for field outUbx in bitmask outProtoMask
#define UBX_CFG_PRT_UART_OUTPROTOMASK_OUTUBX_GET(val)  (U)(((val)&UBX_CFG_PRT_UART_OUTPROTOMASK_OUTUBX_MASK)>>0)  //!< Get outUbx from bitmask outProtoMask
#define UBX_CFG_PRT_UART_OUTPROTOMASK_OUTNMEA_MASK 0x0002  //!< Mask for field outNmea in bitmask outProtoMask
#define UBX_CFG_PRT_UART_OUTPROTOMASK_OUTNMEA_GET(val)  (U)(((val)&UBX_CFG_PRT_UART_OUTPROTOMASK_OUTNMEA_MASK)>>1)  //!< Get outNmea from bitmask outProtoMask

//@}
//! \name Bit Definitions for #UBX_CFG_PRT_UART_s::flags
//@{
#define UBX_CFG_PRT_UART_FLAGS_EXTENDEDTXTIMEOUT_MASK 0x0002  //!< Mask for field extendedTxTimeout in bitmask flags
#define UBX_CFG_PRT_UART_FLAGS_EXTENDEDTXTIMEOUT_GET(val)  (U)(((val)&UBX_CFG_PRT_UART_FLAGS_EXTENDEDTXTIMEOUT_MASK)>>1)  //!< Get extendedTxTimeout from bitmask flags

//@}


//#define UBXID_CFG_PRT 0x0600  // already defined, see above


//================================================================
//! CFG_PRT_USB: Input/Output
/*!
Port Configuration for USB Port
Several configurations can be concatenated to one input message. In this case the payload length can be a multiple of the normal length (see the other versions of CFG-PRT). Output messages from the module contain only one configuration unit.


This message's id is #UBXID_CFG_PRT
*/
//================================================================

typedef struct UBX_CFG_PRT_USB_s
{
	U1  portID;                   //!< Port Identifier Number (= 3 for USB port)
	U1  reserved1;                //!< <r href='DESC-UBX-Reserved'>Reserved</r>
	X2  txReady;                  //!< TX ready PIN configuration
	U1  reserved2[8];             //!< <r href='DESC-UBX-Reserved'>Reserved</r>
	X2  inProtoMask;              //!< A mask describing which input protocols are active.
	X2  outProtoMask;             //!< A mask describing which output protocols are active.
	U1  reserved3[2];             //!< <r href='DESC-UBX-Reserved'>Reserved</r>
	U1  reserved4[2];             //!< <r href='DESC-UBX-Reserved'>Reserved</r>

} UBX_CFG_PRT_USB_t, *UBX_CFG_PRT_USB_pt;


//! \name Bit Definitions for #UBX_CFG_PRT_USB_s::txReady
//@{
#define UBX_CFG_PRT_USB_TXREADY_EN_MASK 0x00000001  //!< Mask for field en in bitmask txReady
#define UBX_CFG_PRT_USB_TXREADY_EN_GET(val)  (U)(((val)&UBX_CFG_PRT_USB_TXREADY_EN_MASK)>>0)  //!< Get en from bitmask txReady
#define UBX_CFG_PRT_USB_TXREADY_POL_MASK 0x00000002  //!< Mask for field pol in bitmask txReady
#define UBX_CFG_PRT_USB_TXREADY_POL_GET(val)  (U)(((val)&UBX_CFG_PRT_USB_TXREADY_POL_MASK)>>1)  //!< Get pol from bitmask txReady
#define UBX_CFG_PRT_USB_TXREADY_PIN_MASK 0x0000007C  //!< Mask for field pin in bitmask txReady
#define UBX_CFG_PRT_USB_TXREADY_PIN_GET(val)  (U)(((val)&UBX_CFG_PRT_USB_TXREADY_PIN_MASK)>>2)  //!< Get pin from bitmask txReady
#define UBX_CFG_PRT_USB_TXREADY_THRES_MASK 0x0000FF80  //!< Mask for field thres in bitmask txReady
#define UBX_CFG_PRT_USB_TXREADY_THRES_GET(val)  (U)(((val)&UBX_CFG_PRT_USB_TXREADY_THRES_MASK)>>7)  //!< Get thres from bitmask txReady

//@}
//! \name Bit Definitions for #UBX_CFG_PRT_USB_s::inProtoMask
//@{
#define UBX_CFG_PRT_USB_INPROTOMASK_INUBX_MASK 0x0001  //!< Mask for field inUbx in bitmask inProtoMask
#define UBX_CFG_PRT_USB_INPROTOMASK_INUBX_GET(val)  (U)(((val)&UBX_CFG_PRT_USB_INPROTOMASK_INUBX_MASK)>>0)  //!< Get inUbx from bitmask inProtoMask
#define UBX_CFG_PRT_USB_INPROTOMASK_INNMEA_MASK 0x0002  //!< Mask for field inNmea in bitmask inProtoMask
#define UBX_CFG_PRT_USB_INPROTOMASK_INNMEA_GET(val)  (U)(((val)&UBX_CFG_PRT_USB_INPROTOMASK_INNMEA_MASK)>>1)  //!< Get inNmea from bitmask inProtoMask
#define UBX_CFG_PRT_USB_INPROTOMASK_INRTCM_MASK 0x0004  //!< Mask for field inRtcm in bitmask inProtoMask
#define UBX_CFG_PRT_USB_INPROTOMASK_INRTCM_GET(val)  (U)(((val)&UBX_CFG_PRT_USB_INPROTOMASK_INRTCM_MASK)>>2)  //!< Get inRtcm from bitmask inProtoMask

//@}
//! \name Bit Definitions for #UBX_CFG_PRT_USB_s::outProtoMask
//@{
#define UBX_CFG_PRT_USB_OUTPROTOMASK_OUTUBX_MASK 0x0001  //!< Mask for field outUbx in bitmask outProtoMask
#define UBX_CFG_PRT_USB_OUTPROTOMASK_OUTUBX_GET(val)  (U)(((val)&UBX_CFG_PRT_USB_OUTPROTOMASK_OUTUBX_MASK)>>0)  //!< Get outUbx from bitmask outProtoMask
#define UBX_CFG_PRT_USB_OUTPROTOMASK_OUTNMEA_MASK 0x0002  //!< Mask for field outNmea in bitmask outProtoMask
#define UBX_CFG_PRT_USB_OUTPROTOMASK_OUTNMEA_GET(val)  (U)(((val)&UBX_CFG_PRT_USB_OUTPROTOMASK_OUTNMEA_MASK)>>1)  //!< Get outNmea from bitmask outProtoMask

//@}


//#define UBXID_CFG_PRT 0x0600  // already defined, see above


//================================================================
//! CFG_PRT_SPI: Input/Output
/*!
Port Configuration for SPI Port
Several configurations can be concatenated to one input message. In this case the payload length can be a multiple of the normal length (see the other versions of CFG-PRT). Output messages from the module contain only one configuration unit.


This message's id is #UBXID_CFG_PRT
*/
//================================================================

typedef struct UBX_CFG_PRT_SPI_s
{
	U1  portID;                   //!< Port Identifier Number (= 4 for SPI port)
	U1  reserved1;                //!< <r href='DESC-UBX-Reserved'>Reserved</r>
	X2  txReady;                  //!< TX ready PIN configuration
	X4  mode;                     //!< SPI Mode Flags
	U1  reserved2[4];             //!< <r href='DESC-UBX-Reserved'>Reserved</r>
	X2  inProtoMask;              //!< A mask describing which input protocols are active.
	X2  outProtoMask;             //!< A mask describing which output protocols are active.
	X2  flags;                    //!< Flags bit mask
	U1  reserved3[2];             //!< <r href='DESC-UBX-Reserved'>Reserved</r>

} UBX_CFG_PRT_SPI_t, *UBX_CFG_PRT_SPI_pt;


//! \name Bit Definitions for #UBX_CFG_PRT_SPI_s::txReady
//@{
#define UBX_CFG_PRT_SPI_TXREADY_EN_MASK 0x00000001  //!< Mask for field en in bitmask txReady
#define UBX_CFG_PRT_SPI_TXREADY_EN_GET(val)  (U)(((val)&UBX_CFG_PRT_SPI_TXREADY_EN_MASK)>>0)  //!< Get en from bitmask txReady
#define UBX_CFG_PRT_SPI_TXREADY_POL_MASK 0x00000002  //!< Mask for field pol in bitmask txReady
#define UBX_CFG_PRT_SPI_TXREADY_POL_GET(val)  (U)(((val)&UBX_CFG_PRT_SPI_TXREADY_POL_MASK)>>1)  //!< Get pol from bitmask txReady
#define UBX_CFG_PRT_SPI_TXREADY_PIN_MASK 0x0000007C  //!< Mask for field pin in bitmask txReady
#define UBX_CFG_PRT_SPI_TXREADY_PIN_GET(val)  (U)(((val)&UBX_CFG_PRT_SPI_TXREADY_PIN_MASK)>>2)  //!< Get pin from bitmask txReady
#define UBX_CFG_PRT_SPI_TXREADY_THRES_MASK 0x0000FF80  //!< Mask for field thres in bitmask txReady
#define UBX_CFG_PRT_SPI_TXREADY_THRES_GET(val)  (U)(((val)&UBX_CFG_PRT_SPI_TXREADY_THRES_MASK)>>7)  //!< Get thres from bitmask txReady

//@}
//! \name Bit Definitions for #UBX_CFG_PRT_SPI_s::mode
//@{
#define UBX_CFG_PRT_SPI_MODE_SPIMODE_MASK 0x00000006  //!< Mask for field spiMode in bitmask mode
#define UBX_CFG_PRT_SPI_MODE_SPIMODE_GET(val)  (U)(((val)&UBX_CFG_PRT_SPI_MODE_SPIMODE_MASK)>>1)  //!< Get spiMode from bitmask mode
#define UBX_CFG_PRT_SPI_MODE_FLOWCONTROL_MASK 0x00000040  //!< Mask for field flowControl in bitmask mode
#define UBX_CFG_PRT_SPI_MODE_FLOWCONTROL_GET(val)  (U)(((val)&UBX_CFG_PRT_SPI_MODE_FLOWCONTROL_MASK)>>6)  //!< Get flowControl from bitmask mode
#define UBX_CFG_PRT_SPI_MODE_FFCNT_MASK 0x00003F00  //!< Mask for field ffCnt in bitmask mode
#define UBX_CFG_PRT_SPI_MODE_FFCNT_GET(val)  (U)(((val)&UBX_CFG_PRT_SPI_MODE_FFCNT_MASK)>>8)  //!< Get ffCnt from bitmask mode

//@}
//! \name Bit Definitions for #UBX_CFG_PRT_SPI_s::inProtoMask
//@{
#define UBX_CFG_PRT_SPI_INPROTOMASK_INUBX_MASK 0x0001  //!< Mask for field inUbx in bitmask inProtoMask
#define UBX_CFG_PRT_SPI_INPROTOMASK_INUBX_GET(val)  (U)(((val)&UBX_CFG_PRT_SPI_INPROTOMASK_INUBX_MASK)>>0)  //!< Get inUbx from bitmask inProtoMask
#define UBX_CFG_PRT_SPI_INPROTOMASK_INNMEA_MASK 0x0002  //!< Mask for field inNmea in bitmask inProtoMask
#define UBX_CFG_PRT_SPI_INPROTOMASK_INNMEA_GET(val)  (U)(((val)&UBX_CFG_PRT_SPI_INPROTOMASK_INNMEA_MASK)>>1)  //!< Get inNmea from bitmask inProtoMask
#define UBX_CFG_PRT_SPI_INPROTOMASK_INRTCM_MASK 0x0004  //!< Mask for field inRtcm in bitmask inProtoMask
#define UBX_CFG_PRT_SPI_INPROTOMASK_INRTCM_GET(val)  (U)(((val)&UBX_CFG_PRT_SPI_INPROTOMASK_INRTCM_MASK)>>2)  //!< Get inRtcm from bitmask inProtoMask

//@}
//! \name Bit Definitions for #UBX_CFG_PRT_SPI_s::outProtoMask
//@{
#define UBX_CFG_PRT_SPI_OUTPROTOMASK_OUTUBX_MASK 0x0001  //!< Mask for field outUbx in bitmask outProtoMask
#define UBX_CFG_PRT_SPI_OUTPROTOMASK_OUTUBX_GET(val)  (U)(((val)&UBX_CFG_PRT_SPI_OUTPROTOMASK_OUTUBX_MASK)>>0)  //!< Get outUbx from bitmask outProtoMask
#define UBX_CFG_PRT_SPI_OUTPROTOMASK_OUTNMEA_MASK 0x0002  //!< Mask for field outNmea in bitmask outProtoMask
#define UBX_CFG_PRT_SPI_OUTPROTOMASK_OUTNMEA_GET(val)  (U)(((val)&UBX_CFG_PRT_SPI_OUTPROTOMASK_OUTNMEA_MASK)>>1)  //!< Get outNmea from bitmask outProtoMask

//@}
//! \name Bit Definitions for #UBX_CFG_PRT_SPI_s::flags
//@{
#define UBX_CFG_PRT_SPI_FLAGS_EXTENDEDTXTIMEOUT_MASK 0x0002  //!< Mask for field extendedTxTimeout in bitmask flags
#define UBX_CFG_PRT_SPI_FLAGS_EXTENDEDTXTIMEOUT_GET(val)  (U)(((val)&UBX_CFG_PRT_SPI_FLAGS_EXTENDEDTXTIMEOUT_MASK)>>1)  //!< Get extendedTxTimeout from bitmask flags

//@}


//#define UBXID_CFG_PRT 0x0600  // already defined, see above


//================================================================
//! CFG_PRT_DDC: Input/Output
/*!
Port Configuration for DDC Port
Several configurations can be concatenated to one input message. In this case the payload length can be a multiple of the normal length (see the other versions of CFG-PRT). Output messages from the module contain only one configuration unit.


This message's id is #UBXID_CFG_PRT
*/
//================================================================

typedef struct UBX_CFG_PRT_DDC_s
{
	U1  portID;                   //!< Port Identifier Number (= 0 for DDC port)
	U1  reserved1;                //!< <r href='DESC-UBX-Reserved'>Reserved</r>
	X2  txReady;                  //!< TX ready PIN configuration
	X4  mode;                     //!< DDC Mode Flags
	U1  reserved2[4];             //!< <r href='DESC-UBX-Reserved'>Reserved</r>
	X2  inProtoMask;              //!< A mask describing which input protocols are active.
	X2  outProtoMask;             //!< A mask describing which output protocols are active.
	X2  flags;                    //!< Flags bit mask
	U1  reserved3[2];             //!< <r href='DESC-UBX-Reserved'>Reserved</r>

} UBX_CFG_PRT_DDC_t, *UBX_CFG_PRT_DDC_pt;


//! \name Bit Definitions for #UBX_CFG_PRT_DDC_s::txReady
//@{
#define UBX_CFG_PRT_DDC_TXREADY_EN_MASK 0x00000001  //!< Mask for field en in bitmask txReady
#define UBX_CFG_PRT_DDC_TXREADY_EN_GET(val)  (U)(((val)&UBX_CFG_PRT_DDC_TXREADY_EN_MASK)>>0)  //!< Get en from bitmask txReady
#define UBX_CFG_PRT_DDC_TXREADY_POL_MASK 0x00000002  //!< Mask for field pol in bitmask txReady
#define UBX_CFG_PRT_DDC_TXREADY_POL_GET(val)  (U)(((val)&UBX_CFG_PRT_DDC_TXREADY_POL_MASK)>>1)  //!< Get pol from bitmask txReady
#define UBX_CFG_PRT_DDC_TXREADY_PIN_MASK 0x0000007C  //!< Mask for field pin in bitmask txReady
#define UBX_CFG_PRT_DDC_TXREADY_PIN_GET(val)  (U)(((val)&UBX_CFG_PRT_DDC_TXREADY_PIN_MASK)>>2)  //!< Get pin from bitmask txReady
#define UBX_CFG_PRT_DDC_TXREADY_THRES_MASK 0x0000FF80  //!< Mask for field thres in bitmask txReady
#define UBX_CFG_PRT_DDC_TXREADY_THRES_GET(val)  (U)(((val)&UBX_CFG_PRT_DDC_TXREADY_THRES_MASK)>>7)  //!< Get thres from bitmask txReady

//@}
//! \name Bit Definitions for #UBX_CFG_PRT_DDC_s::mode
//@{
#define UBX_CFG_PRT_DDC_MODE_SLAVEADDR_MASK 0x000000FE  //!< Mask for field slaveAddr in bitmask mode
#define UBX_CFG_PRT_DDC_MODE_SLAVEADDR_GET(val)  (U)(((val)&UBX_CFG_PRT_DDC_MODE_SLAVEADDR_MASK)>>1)  //!< Get slaveAddr from bitmask mode

//@}
//! \name Bit Definitions for #UBX_CFG_PRT_DDC_s::inProtoMask
//@{
#define UBX_CFG_PRT_DDC_INPROTOMASK_INUBX_MASK 0x0001  //!< Mask for field inUbx in bitmask inProtoMask
#define UBX_CFG_PRT_DDC_INPROTOMASK_INUBX_GET(val)  (U)(((val)&UBX_CFG_PRT_DDC_INPROTOMASK_INUBX_MASK)>>0)  //!< Get inUbx from bitmask inProtoMask
#define UBX_CFG_PRT_DDC_INPROTOMASK_INNMEA_MASK 0x0002  //!< Mask for field inNmea in bitmask inProtoMask
#define UBX_CFG_PRT_DDC_INPROTOMASK_INNMEA_GET(val)  (U)(((val)&UBX_CFG_PRT_DDC_INPROTOMASK_INNMEA_MASK)>>1)  //!< Get inNmea from bitmask inProtoMask
#define UBX_CFG_PRT_DDC_INPROTOMASK_INRTCM_MASK 0x0004  //!< Mask for field inRtcm in bitmask inProtoMask
#define UBX_CFG_PRT_DDC_INPROTOMASK_INRTCM_GET(val)  (U)(((val)&UBX_CFG_PRT_DDC_INPROTOMASK_INRTCM_MASK)>>2)  //!< Get inRtcm from bitmask inProtoMask

//@}
//! \name Bit Definitions for #UBX_CFG_PRT_DDC_s::outProtoMask
//@{
#define UBX_CFG_PRT_DDC_OUTPROTOMASK_OUTUBX_MASK 0x0001  //!< Mask for field outUbx in bitmask outProtoMask
#define UBX_CFG_PRT_DDC_OUTPROTOMASK_OUTUBX_GET(val)  (U)(((val)&UBX_CFG_PRT_DDC_OUTPROTOMASK_OUTUBX_MASK)>>0)  //!< Get outUbx from bitmask outProtoMask
#define UBX_CFG_PRT_DDC_OUTPROTOMASK_OUTNMEA_MASK 0x0002  //!< Mask for field outNmea in bitmask outProtoMask
#define UBX_CFG_PRT_DDC_OUTPROTOMASK_OUTNMEA_GET(val)  (U)(((val)&UBX_CFG_PRT_DDC_OUTPROTOMASK_OUTNMEA_MASK)>>1)  //!< Get outNmea from bitmask outProtoMask

//@}
//! \name Bit Definitions for #UBX_CFG_PRT_DDC_s::flags
//@{
#define UBX_CFG_PRT_DDC_FLAGS_EXTENDEDTXTIMEOUT_MASK 0x0002  //!< Mask for field extendedTxTimeout in bitmask flags
#define UBX_CFG_PRT_DDC_FLAGS_EXTENDEDTXTIMEOUT_GET(val)  (U)(((val)&UBX_CFG_PRT_DDC_FLAGS_EXTENDEDTXTIMEOUT_MASK)>>1)  //!< Get extendedTxTimeout from bitmask flags

//@}


//#define UBXID_CFG_PRT 0x0600  // already defined, see above


//================================================================
//! CFG_PWR_DATA1: Set
/*!
Put receiver in a defined power state
-


This message's id is #UBXID_CFG_PWR
*/
//================================================================

typedef struct UBX_CFG_PWR_DATA1_s
{
	U1  version;                  //!< Message version (1 for this version)
	U1  reserved1[3];             //!< <r href='DESC-UBX-Reserved'>Reserved</r>
	U4  state;                    //!< Enter system state

} UBX_CFG_PWR_DATA1_t, *UBX_CFG_PWR_DATA1_pt;


#define UBXID_CFG_PWR 0x0657 //!< message id for CFG-PWR
	

//================================================================
//! CFG_RATE_POLL0: Poll Request
/*!
Poll Navigation/Measurement Rate Settings
Sending this (empty / no-payload) message to the receiver results in the receiver returning a message of type CFG-RATE with a payload as defined below


This message's id is #UBXID_CFG_RATE
*/
//================================================================

typedef struct UBX_CFG_RATE_POLL0_s
{

} UBX_CFG_RATE_POLL0_t, *UBX_CFG_RATE_POLL0_pt;


#define UBXID_CFG_RATE 0x0608 //!< message id for CFG-RATE
	

//================================================================
//! CFG_RATE_DATA0: Input/Output
/*!
Navigation/Measurement Rate Settings
The u-blox positioning technology supports navigation update rates higher or lower than 1 update per second. The calculation of the navigation solution will always be aligned to the top of a second.
* The update rate has a direct influence on the power consumption. The more fixes that are required, the more CPU power and communication resources are required.
* For most applications a 1 Hz update rate would be sufficient.
* When using Power Save Mode, measurement and navigation rate can differ from the values configured here. See <r href=\"PM-DESC-MEASNAVRATE'>Measurement and navigation rate with Power Save Mode</r> for details.

   \note: This feature is not supported for the FTS product variant.

This message's id is #UBXID_CFG_RATE
*/
//================================================================

typedef struct UBX_CFG_RATE_DATA0_s
{
	U2  measRate;                 //!< Measurement Rate, GPS measurements are taken every measRate milliseconds
	U2  navRate;                  //!< Navigation Rate, in number of measurement cycles. This parameter cannot be changed, and must be set to 1.
	U2  timeRef;                  //!< Alignment to reference time

} UBX_CFG_RATE_DATA0_t, *UBX_CFG_RATE_DATA0_pt;


//#define UBXID_CFG_RATE 0x0608  // already defined, see above


//================================================================
//! CFG_RINV_POLL0: Poll Request
/*!
Poll contents of Remote Inventory
-


This message's id is #UBXID_CFG_RINV
*/
//================================================================

typedef struct UBX_CFG_RINV_POLL0_s
{

} UBX_CFG_RINV_POLL0_t, *UBX_CFG_RINV_POLL0_pt;


#define UBXID_CFG_RINV 0x0634 //!< message id for CFG-RINV
	

//================================================================
//! CFG_RINV_DATA0: Input/Output
/*!
Contents of Remote Inventory
If <i>N</i> is greater than 30, the excess bytes are discarded. In future firmware versions, this limit may change.


This message's id is #UBXID_CFG_RINV
*/
//================================================================

typedef struct UBX_CFG_RINV_DATA0_s
{
	X1  flags;                    //!< Flags
	//REPEAT: UBX_CFG_RINV_DATA0_DATA_t repeat0[N];              

} UBX_CFG_RINV_DATA0_t, *UBX_CFG_RINV_DATA0_pt;


//! \name Bit Definitions for #UBX_CFG_RINV_DATA0_s::flags
//@{
#define UBX_CFG_RINV_DATA0_FLAGS_DUMP_MASK 0x1  //!< Mask for field dump in bitmask flags
#define UBX_CFG_RINV_DATA0_FLAGS_DUMP_GET(val)  (U)(((val)&UBX_CFG_RINV_DATA0_FLAGS_DUMP_MASK)>>0)  //!< Get dump from bitmask flags
#define UBX_CFG_RINV_DATA0_FLAGS_BINARY_MASK 0x2  //!< Mask for field binary in bitmask flags
#define UBX_CFG_RINV_DATA0_FLAGS_BINARY_GET(val)  (U)(((val)&UBX_CFG_RINV_DATA0_FLAGS_BINARY_MASK)>>1)  //!< Get binary from bitmask flags

//@}


//! Optional Sub-Structure of #UBX_CFG_RINV_DATA0_t
typedef struct UBX_CFG_RINV_DATA0_DATA_s
{
	U1  data;                     //!< Data to store/stored in Remote Inventory

} UBX_CFG_RINV_DATA0_DATA_t, *UBX_CFG_RINV_DATA0_DATA_pt;



//#define UBXID_CFG_RINV 0x0634  // already defined, see above


//================================================================
//! CFG_RST_DATA3: Command
/*!
Reset Receiver / Clear Backup Data Structures
Don't expect this message to be acknowledged by the receiver.
* Newer FW version won't acknowledge this message at all.
* Older FW version will acknowledge this message but the acknowledge may not be sent completely before the receiver is reset.


This message's id is #UBXID_CFG_RST
*/
//================================================================

typedef struct UBX_CFG_RST_DATA3_s
{
	X2  navBbrMask;               //!< BBR Sections to clear. The following Special Sets apply:
	U1  resetMode;                //!< Reset Type
	U1  reserved1;                //!< <r href='DESC-UBX-Reserved'>Reserved</r>

} UBX_CFG_RST_DATA3_t, *UBX_CFG_RST_DATA3_pt;


//! \name Bit Definitions for #UBX_CFG_RST_DATA3_s::navBbrMask
//@{
#define UBX_CFG_RST_DATA3_NAVBBRMASK_EPH_MASK 0x0001  //!< Mask for field eph in bitmask navBbrMask
#define UBX_CFG_RST_DATA3_NAVBBRMASK_EPH_GET(val)  (U)(((val)&UBX_CFG_RST_DATA3_NAVBBRMASK_EPH_MASK)>>0)  //!< Get eph from bitmask navBbrMask
#define UBX_CFG_RST_DATA3_NAVBBRMASK_ALM_MASK 0x0002  //!< Mask for field alm in bitmask navBbrMask
#define UBX_CFG_RST_DATA3_NAVBBRMASK_ALM_GET(val)  (U)(((val)&UBX_CFG_RST_DATA3_NAVBBRMASK_ALM_MASK)>>1)  //!< Get alm from bitmask navBbrMask
#define UBX_CFG_RST_DATA3_NAVBBRMASK_HEALTH_MASK 0x0004  //!< Mask for field health in bitmask navBbrMask
#define UBX_CFG_RST_DATA3_NAVBBRMASK_HEALTH_GET(val)  (U)(((val)&UBX_CFG_RST_DATA3_NAVBBRMASK_HEALTH_MASK)>>2)  //!< Get health from bitmask navBbrMask
#define UBX_CFG_RST_DATA3_NAVBBRMASK_KLOB_MASK 0x0008  //!< Mask for field klob in bitmask navBbrMask
#define UBX_CFG_RST_DATA3_NAVBBRMASK_KLOB_GET(val)  (U)(((val)&UBX_CFG_RST_DATA3_NAVBBRMASK_KLOB_MASK)>>3)  //!< Get klob from bitmask navBbrMask
#define UBX_CFG_RST_DATA3_NAVBBRMASK_POS_MASK 0x0010  //!< Mask for field pos in bitmask navBbrMask
#define UBX_CFG_RST_DATA3_NAVBBRMASK_POS_GET(val)  (U)(((val)&UBX_CFG_RST_DATA3_NAVBBRMASK_POS_MASK)>>4)  //!< Get pos from bitmask navBbrMask
#define UBX_CFG_RST_DATA3_NAVBBRMASK_CLKD_MASK 0x0020  //!< Mask for field clkd in bitmask navBbrMask
#define UBX_CFG_RST_DATA3_NAVBBRMASK_CLKD_GET(val)  (U)(((val)&UBX_CFG_RST_DATA3_NAVBBRMASK_CLKD_MASK)>>5)  //!< Get clkd from bitmask navBbrMask
#define UBX_CFG_RST_DATA3_NAVBBRMASK_OSC_MASK 0x0040  //!< Mask for field osc in bitmask navBbrMask
#define UBX_CFG_RST_DATA3_NAVBBRMASK_OSC_GET(val)  (U)(((val)&UBX_CFG_RST_DATA3_NAVBBRMASK_OSC_MASK)>>6)  //!< Get osc from bitmask navBbrMask
#define UBX_CFG_RST_DATA3_NAVBBRMASK_UTC_MASK 0x0080  //!< Mask for field utc in bitmask navBbrMask
#define UBX_CFG_RST_DATA3_NAVBBRMASK_UTC_GET(val)  (U)(((val)&UBX_CFG_RST_DATA3_NAVBBRMASK_UTC_MASK)>>7)  //!< Get utc from bitmask navBbrMask
#define UBX_CFG_RST_DATA3_NAVBBRMASK_RTC_MASK 0x0100  //!< Mask for field rtc in bitmask navBbrMask
#define UBX_CFG_RST_DATA3_NAVBBRMASK_RTC_GET(val)  (U)(((val)&UBX_CFG_RST_DATA3_NAVBBRMASK_RTC_MASK)>>8)  //!< Get rtc from bitmask navBbrMask
#define UBX_CFG_RST_DATA3_NAVBBRMASK_AOP_MASK 0x8000  //!< Mask for field aop in bitmask navBbrMask
#define UBX_CFG_RST_DATA3_NAVBBRMASK_AOP_GET(val)  (U)(((val)&UBX_CFG_RST_DATA3_NAVBBRMASK_AOP_MASK)>>15)  //!< Get aop from bitmask navBbrMask

//@}


#define UBXID_CFG_RST 0x0604 //!< message id for CFG-RST
	

//================================================================
//! CFG_RXM_POLL0: Poll Request
/*!
Poll RXM configuration
Upon sending of this message, the receiver returns CFG-RXM as defined below


This message's id is #UBXID_CFG_RXM
*/
//================================================================

typedef struct UBX_CFG_RXM_POLL0_s
{

} UBX_CFG_RXM_POLL0_t, *UBX_CFG_RXM_POLL0_pt;


#define UBXID_CFG_RXM 0x0611 //!< message id for CFG-RXM
	

//================================================================
//! CFG_RXM_DATA1: Input/Output
/*!
RXM configuration
For a detailed description see section <r href=\"CFG-PM-DESC'>Power Management</r>.
Note that Power Save Mode cannot be selected when the receiver is configured to process GLONASS signals (using <rc href=\"UBX-CFG-GNSS'>CFG-GNSS</rc>).


This message's id is #UBXID_CFG_RXM
*/
//================================================================

typedef struct UBX_CFG_RXM_DATA1_s
{
	U1  reserved1;                //!< <r href='DESC-UBX-Reserved'>Reserved</r>
	U1  lpMode;                   //!< Low Power Mode

} UBX_CFG_RXM_DATA1_t, *UBX_CFG_RXM_DATA1_pt;


//#define UBXID_CFG_RXM 0x0611  // already defined, see above


//================================================================
//! CFG_SBAS_POLL0: Poll Request
/*!
Poll contents of SBAS Configuration
-


This message's id is #UBXID_CFG_SBAS
*/
//================================================================

typedef struct UBX_CFG_SBAS_POLL0_s
{

} UBX_CFG_SBAS_POLL0_t, *UBX_CFG_SBAS_POLL0_pt;


#define UBXID_CFG_SBAS 0x0616 //!< message id for CFG-SBAS
	

//================================================================
//! CFG_SBAS_U5: Input/Output
/*!
SBAS Configuration
This message configures the SBAS receiver subsystem (i.e. WAAS, EGNOS, MSAS). See the <r href=\"CFG-SBAS-DESC'>SBAS Configuration Settings Description</r> for a detailed description of how these settings affect receiver operation.


This message's id is #UBXID_CFG_SBAS
*/
//================================================================

typedef struct UBX_CFG_SBAS_U5_s
{
	X1  mode;                     //!< SBAS Mode
	X1  usage;                    //!< SBAS Usage
	U1  maxSBAS;                  //!< Maximum Number of SBAS prioritized tracking channels (valid range: 0 - 3) to use (obsolete and superseeded by UBX-CFG-GNSS in <r href='ProtocolVersions'>protocol versions 14+</r>).
	X1  scanmode2;                //!< Continuation of scanmode bitmask below
	X4  scanmode1;                //!< Which SBAS PRN numbers to search for (Bitmask)

} UBX_CFG_SBAS_U5_t, *UBX_CFG_SBAS_U5_pt;
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
